lonesoulsurfer/Acid_Drip_Bassline_and_Drum_Synth/src/Acid_Drip_Drum_Acid_Drift_V5/Acid_Drip_Drum_Acid_Drift_V5.ino

/*
 * =====================================================================
 *              Acid Drip - RP2040 Acid Bassline Synthesizer
 *              Synthesis engine ported from reference "Badass Bass"
 * =====================================================================
 *
 * BUTTON LAYOUT (2 rows of 8 pads):
 *
 *   ┌─────┬─────┬─────┬─────┬─────┬─────┬──────┬──────┐
 *   │  1  │  2  │  3  │  4  │  5  │  6  │  7   │  8   │
 *   │step │step │step │step │step │step │step  │step  │
 *   │ 1   │ 2   │ 3   │ 4   │ 5   │ 6   │ 7    │ 8    │
 *   ├─────┼─────┼─────┼─────┼─────┼─────┼──────┼──────┤
 *   │  9  │ 10  │ 11  │ 12  │ 13  │ 14  │  15  │  16  │
 *   │KEY  │RIFF │SOUND│WALK │ FX  │TEMPO│PLEN  │PAT>  │
 *   └─────┴─────┴─────┴─────┴─────┴─────┴──────┴──────┘
 *   (bottom row labels only visible in FUNC mode)
 *

 * PAD FUNCTIONS (normal mode):
 *   Short press         : Toggle step on/off
 *   Long press ×1       : Toggle accent
 *   Long press ×2       : Toggle glide
 *   Hold + CUT pot      : Set step note (scale-quantised)
 *   All 16 pads are full steps — no dedicated buttons
 *
 * CHORD: PLAY (pads 1+2 simultaneously):
 *   Start / Stop sequencer
 *   Long hold (1s+)     : Factory reset
 *
 * CHORD: FUNC (pads 7+8 simultaneously):
 *   Toggle FUNC mode on/off
 *   Exits FX assign sub-mode if active
 *
 * SAVE / LOAD (while holding pads 7+8):
 *   Tap pad 3/4/5/6     : Load slot 1/2/3/4 — restores acid pattern, DRIFT,
 *                         and drum beat together, whichever of the three
 *                         actually have data saved in that slot
 *   Hold pad 3/4/5/6    : Save slot 1/2/3/4 (1 second hold) — captures
 *                         acid + DRIFT + drums together into that slot,
 *                         whatever each currently has dialled in. Same
 *                         gesture works from the drum screen too — either
 *                         screen saves/loads all three.
 *   Slot status shown as dots top-right of screen (yellow=saved, grey=empty)
 *
 * FUNC MODE (pads 7+8 to enter/exit):
 *   Bottom row pads 9-16 select a function (labels shown on screen):
 *     Pad 9  = KEY    — top row pads 1-8 select root note (C D Eb F G Ab Bb B)
 *     Pad 10 = RIFF   — pads 1-8 select preset riff pattern (DFLT/SQNCE/FUNK/MINI/JUMP/RAVE/SYNC/DARK)
 *     Pad 11 = SOUND  — top row pads 1-8 select synth voice
 *     Pad 12 = WALK   — top row pads 1-8 select note walk mode
 *                        p1=OFF  p2=4TH    p3=OCTWAVE p4=5TH
 *                        p5=BOUNCE  p6=MIN3RD  p7=VAMP3  p8=RANDOM
 *     Pad 13 = FX     — enters FX ASSIGN sub-mode
 *     Pad 14 = TEMPO  — top row pads 1-8 select preset BPM (100/110/120/128/133/138/145/160)
 *                        tap TEMPO pad repeatedly to set BPM by tap-tempo
 *     Pad 15 = PLEN   — top row pads 1-8 set length 1-8
 *                        bottom row pads 9-16 set length 9-16
 *     Pad 16 = PAT>   — top row pads 1-8 select pattern play mode:
 *                        p1=FWD  p2=CW (fwd then rev)  p3=ALT (odd/even)  p4=REV
 *                        p5=SKIP2 (every 2nd)  p6=SKIP3 (every 3rd)  p7=PING  p8=RND
 *
 * FX ASSIGN SUB-MODE (FUNC → pad 13):
 *   Phase 1: press top-row pads 1-8 to select an effect:
 *     Pad 1=None  Pad 2=Oct Up  Pad 3=Retrigger  Pad 4=Stutter
 *     Pad 5=Maj Step  Pad 6=Min Step  Pad 7=Dom7 Step  Pad 8=Dim Step
 *   Phase 2: press any pad 1-16 to assign that effect to that step
 *   Tap selected FX pad again to deselect
 *   Long-hold pad 1 = clear all step effects
 *   Pads 7+8 chord = exit FX assign to main screen
 *
 * EASTER EGG: ACID WALKS (pads 11+12+13+14, hold 1s):
 *   Toggles a hidden bank of 8 patterns inspired by classic acid/house
 *   tracks, each with its own preset key/tempo/length/sound.
 *   Pads 1-8 select a pattern. FUNC mode, FX assign, and drum mode all
 *   continue to work normally while active. Hold the same chord again
 *   to exit back to the normal pattern.
 *
 * ACCENT EDIT (pads 15+16, hold 1s):
 *   Toggles a mode where CUT/RES/DCY tune the accent envelope itself
 *   instead of the live filter:
 *     CUT = accent peak cutoff boost   RES = accent peak resonance boost
 *     DCY = accent decay-time (CCW=short/snappy, CW=long/dramatic)
 *   Normal CUT/RES/DCY values freeze while tuning. Hold the chord again
 *   to exit — settings save to EEPROM automatically and persist across
 *   power cycles until changed again.
 *
 * WIRING:
 *   TFT   : SCK=GP6, SDA=GP7, RST=GP8, DC=GP10, CS=GP13
 *   Pots  : CUT=GP26, RES=GP27, DCY=GP28
 *   Sync  : IN=GP2 (hold pad 14 at power-on to boot into Sync In mode)
 *   Audio : GP15 (100R + 10nF RC filter to output jack)
 *
 *   Pads (top row, steps 1-8 / FUNC apply):
 *     GP14=pad1  GP12=pad2  GP11=pad3  GP16=pad4
 *     GP17=pad5  GP19=pad6  GP20=pad7  GP21=pad8
 *
 *   Pads (bottom row, steps 9-16 / FUNC select):
 *     GP0=pad9   GP1=pad10  GP3=pad11  GP4=pad12
 *     GP5=pad13  GP9=pad14  GP18=pad15 GP22=pad16
 *
 * =====================================================================
 */

// =====================================================================
// MOZZI CONFIG - must precede all includes
// =====================================================================
#include "MozziConfigValues.h"
#define MOZZI_AUDIO_MODE     MOZZI_OUTPUT_PWM
#define MOZZI_ANALOG_READ    MOZZI_ANALOG_READ_NONE
#define MOZZI_AUDIO_PIN_1    15
#define MOZZI_AUDIO_RATE     16384
#define MOZZI_CONTROL_RATE   256

#include <Mozzi.h>
#include <SPI.h>
#include <Adafruit_GFX.h>
#include <Adafruit_ILI9341.h>
#include <EEPROM.h>
#include <math.h>   // expf/logf — ch2's decay-time-to-multiplier calc in triggerCh2Pulse()

// =====================================================================
// BENCH INSTRUMENTATION — TEMPORARY, pre-CHORD-engine only.
// =====================================================================
// Measures real spare headroom on core 0's audio path (this file's
// updateAudio(), GP15/acid) and core 1's audio path
// (BeatMachine2.ino's bmFillDrumBufferTo(), GP2/drift+drums) BEFORE any
// new engine work starts, so "how much CPU is actually free" is a
// measurement, not a guess.
//
// Deliberately does NOT touch flash-resident code from inside the
// __not_in_flash_func() audio functions: time_us_32() is a pico-sdk
// static inline that reads the hardware timer register directly (no
// call into flash), so it's safe to use here for the same reason the
// rest of updateAudio()/bmFillDrumBufferTo() has to stay flash-free —
// see the XIP-contention notes elsewhere in this file. Reporting
// (Serial prints, float math) happens ONLY from loop1() on core 1,
// never inside the timed sections themselves, so the act of measuring
// doesn't perturb what's being measured.
//
// Remove or set to 0 once the CHORD engine's core-placement and voice
// budget are decided — this isn't meant to ship.
#define BENCH_AUDIO_HEADROOM 1

#if BENCH_AUDIO_HEADROOM
#include "pico/time.h"

// One "window" = one second's worth of audio-rate samples, so reported
// numbers are already per-second — easy to eyeball without maths.
#define BENCH_WINDOW_SAMPLES MOZZI_AUDIO_RATE

// ---- core 0 (updateAudio / GP15 / acid) — written ONLY on core 0 ----
static uint32_t bench0_windowStart    = 0;
static uint32_t bench0_callsInWindow  = 0;
static uint32_t bench0_sumUsInWindow  = 0;
static uint32_t bench0_maxUsInWindow  = 0;

// Latest-window snapshot — updated once/sec, read by core 1's reporter.
// A torn read here costs at worst one stale field for one report cycle;
// this is a debug counter, not anything audio-critical, so that's fine.
volatile uint32_t bench0_avgUs  = 0;
volatile uint32_t bench0_maxUs  = 0;
volatile uint32_t bench0_callHz = 0;

// Call at the very top of updateAudio(), before any early return, so
// silent/idle samples still count — an average that only sees "busy"
// samples would understate real headroom.
static inline void __not_in_flash_func(benchAudioEnter)(uint32_t &t0) {
  t0 = time_us_32();
}

// Call at EVERY return point of updateAudio(), passing the t0 from
// benchAudioEnter(). No branches beyond the once-per-window reset, no
// allocation — kept cheap on purpose since this runs every sample.
static inline void __not_in_flash_func(benchAudioExit)(uint32_t t0) {
  uint32_t dt = time_us_32() - t0;
  bench0_callsInWindow++;
  bench0_sumUsInWindow += dt;
  if (dt > bench0_maxUsInWindow) bench0_maxUsInWindow = dt;
  if (bench0_callsInWindow >= BENCH_WINDOW_SAMPLES) {
    bench0_avgUs = bench0_sumUsInWindow / bench0_callsInWindow;
    bench0_maxUs = bench0_maxUsInWindow;
    uint32_t now  = time_us_32();
    uint32_t span = now - bench0_windowStart;   // real elapsed us this window
    bench0_callHz = span ? (bench0_callsInWindow * 1000000UL) / span : 0;
    bench0_windowStart   = now;
    bench0_callsInWindow = 0;
    bench0_sumUsInWindow = 0;
    bench0_maxUsInWindow = 0;
  }
}
#endif // BENCH_AUDIO_HEADROOM

// ── Beat Machine 2 — forward declarations ────────────────────────────
extern bool   bmMode;
extern bool   bmFullDirty;
extern void   bmInit();
extern void   bmUpdateControl();
extern void   bmDoDraw();
extern void   bmStartAudio();
int32_t       __not_in_flash_func(ch2RenderSample)();   // DRIFT render — defined in Drift.ino; RAM-resident, see there
extern bool   bmAlarmStarted;  // true once GP2 audio hardware is initialized —
                               // gates every bmFillDrumBuffer call (NOT debug)
extern void   bmClearPadState();
extern bool   bmPotLocked;
extern uint8_t bmPotPickup;
extern void     bmTriggerStep(uint8_t step);
extern byte     bmStepDiv;
extern byte     bmPulseNum;
extern uint16_t bmStepNum;
extern byte     bmDrumPos;
extern bool   bmPlaying;
extern bool   bmPlayChanged;
extern void   bmFillDrumBuffer();
extern int32_t bmRenderDrumSample();  // one drum-bus sample (GP15 fold-in for sync mode)
extern void   bmFillDrumBufferMax();  // full pre-fill — ONLY for EEPROM.commit() (both cores
                                      // stall during flash erase, fills can't be threaded).
                                      // Never use before draws: see bmFillScreenFed()
extern void   bmPrintFed(const char* s);
extern void   bmFillScreenFed(uint16_t color);  // banded full-screen clear — ALWAYS use
                                                // instead of tft.fillScreen() once audio is
                                                // running; the atomic ~103ms clear both
                                                // underruns GP2 and XIP-stalls core 0/Mozzi  // print char-by-char, topping up GP2 between chars —
                                          // REQUIRED for any string over ~20 chars: one atomic
                                          // print() of a long string is 40-80ms of per-pixel GFX
                                          // SPI, which outspends the ring buffer in a single call
extern void   bmDrawDrumFlash();
extern uint32_t bmLastFlashDraw;
extern float    bmStoredTempo;
extern bool     bmPChord[16];
extern bool     bmPState[16];
extern bool     bmP11Deferred;
extern void   bmSavePatch(uint8_t slot);
extern void   bmLoadPatch(uint8_t slot);
extern bool   bmPatchWasPlaying(uint8_t slot);
extern void   bmStartDrums();
extern void   bmStopDrums();
extern bool   bmSlotHasData[4];
extern void   bmCheckSlots();
extern void   bmResetToBasic();

#define BM_SW_A  8   // pad 9 (index 8) — mode switch pad A
#define BM_SW_B  9   // pad 10 (index 9) — mode switch pad B
bool     bmAcidWasRunning = false;  // legacy — no longer used for logic (kept to avoid extern breakage)
// acidPlaying: true when the acid sequencer should fire notes AND render
// on GP15 (see updateAudio() — GP15 is acid-only; DRIFT lives on GP2).
// Independent of bmPlaying and of driftPlaying.
// seq.running = acidPlaying || driftPlaying || bmPlaying — the shared clock
// ticks whenever ANY module wants it, and stopping one never kills another's
// clock.
bool     acidPlaying      = false;

// driftPlaying: DRIFT's own play/stop state, exactly mirroring acidPlaying
// but for the DRIFT voice, which renders on GP2 (bmFillDrumBufferTo() in
// BeatMachine2.ino, summed with drums there) — see the DRIFT OUTPUT
// comment near ch2SynthMode's declaration. Acid and DRIFT can play
// SIMULTANEOUSLY, blended by the PCB's physical mix pot; pads 9+10+11 swap
// ch2SynthMode, which decides which one the pad/pot surface currently
// EDITS, not which one is audible. Each has its own independent play/stop
// state, which is why this can't just reuse acidPlaying: start acid, swap
// edit focus to DRIFT (9+10+11), start DRIFT too (pads 1+2) — both should
// now be audible together (mix pot permitting), and stopping one (pads 1+2
// again) must not touch the other's state.
bool     driftPlaying     = false;


// Easter egg: hold pads 11+12+13+14 (indices 10-13) together for ~1s to
// toggle "Acid Walks" — a value strip of 8 classic-acid-inspired patterns.
#define WALK_PAD_A 10  // pad 11
#define WALK_PAD_B 11  // pad 12
#define WALK_PAD_C 12  // pad 13
#define WALK_PAD_D 13  // pad 14
#define WALK_HOLD_MS 1000
bool     walksMode    = false;  // true while the Acid Walks value strip is shown
bool     walksArmed   = false;  // chord held, waiting for WALK_HOLD_MS
uint32_t walksArmMs   = 0;
uint8_t  curWalk      = 0;      // currently-loaded Acid Walks pattern index

// PATTERN CHAINING: quick double-tap of pads 12+13 (indices 11-12 — reuses
// two of the four WALK pads) toggles between:
//   - chain-build mode: pads 3-6 (slots 1-4) tap-append to a play order,
//     up to 16 positions, repeats allowed
//   - chain playback: on exit, the built chain auto-plays, advancing to
//     the next chain position after each slot's pattern completes one
//     full loop (tick-counted against seq.len, so it works under any
//     rrMode, not just plain FWD)
// Session-only — not saved to EEPROM. Tapping the gesture again at any
// time (whether currently building or currently chain-playing) drops
// whatever chain exists and starts a fresh build.
//
// This DOES collide with the WALK chord in practice, despite reusing only
// 2 of its 4 pads: a real "press all 4 together" gesture routinely lands
// 12+13 within each other's 200ms double-tap window before 11 and 14 also
// register, since WALK's own arm check only looks at whether all 4 are
// down AT THE INSTANT of a press — it has no way to tell "12+13 just
// landed, but this might still be the start of a 4-pad gesture" from "12+13
// was a deliberate standalone double-tap". CHAIN_HOLD_MS below exists
// solely to give WALK's other two pads a chance to prove it's the latter
// before CHAIN commits — see the arm/fire logic in updateControl() and the
// press-time chord check for the reasoning in full.
#define CHAIN_PAD_A WALK_PAD_B  // pad 12
#define CHAIN_PAD_B WALK_PAD_C  // pad 13
#define CHAIN_HOLD_MS 150       // short — long enough for a genuine 4-finger
                                 // WALK attempt to have landed pad 11 and/or
                                 // pad 14 too, short enough that a deliberate
                                 // double-tap toggle still feels immediate
bool     chainMode      = false;  // chain-builder UI/input active
bool     chainArmed     = false;  // 12+13 landed, waiting out CHAIN_HOLD_MS
uint32_t chainArmMs     = 0;
bool     chainActive    = false;  // a built chain is currently playing back
uint8_t  chain[16]      = {0};    // slot index (0-3) per chain position
uint8_t  chainLen       = 0;      // number of filled chain positions
uint8_t  chainPos       = 0;      // current playback position within the chain
uint16_t chainTickCount = 0;      // steps elapsed since the last chain advance

// ACCENT — was previously live-tunable (hold pads 15+16, tweak on CUT/RES/
// DECAY). Locked to a fixed value instead: the difference it made was
// small, and it freed pads 15+16 for MIX EDIT below.
// ---- Filter envelope depth (303 "wah"/squelch sweep) ----------------------
// The squelch is the cutoff ENVELOPE sweeping the filter, not static
// resonance. These set how far the filter opens on note-on before decaying
// back down. They were tiny (30/40 cutoff, 0/200 res) — a nudge, not a sweep —
// which is why hardware never sounded like the reference render. Deepened here.
// IMPORTANT: the envelope ADDS to the CUT pot. For the sweep to be audible you
// must play with the CUT pot LOW (dark rest) so the envelope has room to open
// it — exactly like a real 303 (cutoff down, env-mod up). With CUT high the
// envelope just slams into the 255 ceiling and you hear no wah.
#define ENV_CUTOFF_NORMAL    90    // SEED: normal-note cutoff env peak — sweep depth
#define ENV_RES_NORMAL       50    // normal-note resonance env peak (fixed, not a knob)
#define ACCENT_RES_FIXED    200    // accent peak resonance boost (capped at gResCap in the cascade)
#define ENV_DECAY_NORMAL      5    // SEED: normal env decay divisor (HIGHER = slower/longer sweep)
#define ACCENT_DECAY_FIXED   10    // accent envelope decay divisor (1-20) — "mid"
#define ACID_LPF_RESDIV_SEED 200   // SEED: resonance divisor, moderate default in musical range 150-256

// ---- Runtime-tweakable filter params (SETTINGS mode: hold pads 1+2+3) ------
// These start at the SEED values above and are overwritten by EEPROM on boot
// if a saved block exists. In SETTINGS mode the three pots drive them live:
//   CUT pot   -> gEnvCutNorm  (sweep DEPTH; accent auto-scales to 2x, capped 255)
//   DECAY pot -> gEnvDecayDiv (sweep SPEED; higher divisor = slower "waaow")
//   RES pot   -> gResDiv      (resonance; gResCap auto-tracks at x1.4 so the
//                              cascade can never reach the ~8kHz squeal band)
int16_t gEnvCutNorm  = ENV_CUTOFF_NORMAL;
int16_t gEnvDecayDiv = ENV_DECAY_NORMAL;
int16_t gResDiv      = ACID_LPF_RESDIV_SEED;
int16_t gResCap      = (ACID_LPF_RESDIV_SEED * 7) / 5;   // recomputed whenever gResDiv changes
int16_t gResTrim     = 110;   // HP-filter input body-trim, driven by the front RES pot (110=full body)
// recomputeResCap only feeds the CASCADE fallback's squeal cap now; the HP
// filter's resonance + body-trim come live from the front-panel RES pot
// (gAcidResCoeffQ8 / gResTrim, set in updateControl).
static inline void recomputeResCap() {
  gResCap = (int16_t)((gResDiv * 7) / 5);
}

// ---- SETTINGS mode: hold pads 1 + 9 for ~1s (mirrors MIX EDIT) ------------
// 1 & 9 are physically adjacent and free as a pair — 1+2 is the PLAY chord and
// 9+10 is the LAYER chord, but 1+9 isn't claimed by anything.
#define SET_PAD_A 0    // pad 1
#define SET_PAD_B 8    // pad 9
#define SET_HOLD_MS 1000
bool     setEditMode  = false;   // true while CUT/RES/DECAY pots trim filter params
bool     setEditArmed = false;   // chord held, waiting for SET_HOLD_MS
uint32_t setEditArmMs = 0;
int      setPotSnap[3] = {-1,-1,-1};        // raw pot at entry (soft takeover)
bool     setPotLive[3] = {false,false,false};

// MIX EDIT: hold pads 15+16 (indices 14-15) together for ~1s to toggle a
// mode where the CUT/RES/DECAY pots trim the output level of each of the
// three synth engines independently — CUT=acid, RES=DRIFT, DECAY=drums.
// This is a DIGITAL trim on top of the physical summing pot (which only
// blends acid/GP15 against DRIFT+drums/GP2 as one combined pair) — it's
// what actually lets DRIFT be balanced against drums, which the pot alone
// can't do. Values save to EEPROM on exit, same pattern accent used to.
#define MIX_PAD_A 14  // pad 15
#define MIX_PAD_B 15  // pad 16
#define MIX_HOLD_MS 1000
bool     mixEditMode  = false;  // true while CUT/RES/DECAY pots trim engine levels
bool     mixEditArmed = false;  // chord held, waiting for MIX_HOLD_MS
uint32_t mixEditArmMs = 0;
// POT PICKUP. Without this, entering MIX EDIT snapped all three levels to
// wherever the physical pots happened to be sitting — so the saved mix you
// came in to inspect was destroyed by the act of opening the page, and you
// could not nudge one engine without the other two jumping too. Each pot
// now stays inert until it is MOVED past a threshold from its position at
// entry, so opening MIX EDIT is non-destructive and you adjust exactly the
// engine you touch. Same soft-takeover idea as the drum machine's
// bmFillPotLock/bmFillPotRef pair.
int      mixPotSnap[3] = {-1,-1,-1};   // raw pot at entry; -1 = not yet armed
bool     mixPotLive[3] = {false,false,false};
// Set true while in drum mode. Drums bypass the per-engine pot-ownership
// block (updateControl returns at the bmMode guard, above it), so a
// synth->drums->synth round trip never trips that block's ctx-change test
// and the still-live pots overwrite the stored values on return. This flag
// forces the pickup to re-arm the first time we're back in acid/DRIFT.
bool     gPotCtxReArm = false;
#define  MIX_PICKUP_DELTA 24           // raw ADC counts (~2.3% of travel)
// Same threshold reused by the per-engine pot ownership in updateControl().
#define  POT_PICKUP_DELTA MIX_PICKUP_DELTA
// MIX_UNITY: the raw 0-255 level value that means "unchanged, original
// volume". It is now the SAME for all three engines, so all three pots
// behave identically: unity at 2/3 travel, attenuation below, up to ~1.5x
// boost above.
//
// Acid used to be the exception — unity pinned at the TOP of its travel,
// attenuate-only — because its raw waveform rides close to full 0-255
// scale and any boost hard-clipped into buzzing. That asymmetry is why
// mixing acid felt worse than mixing drums or DRIFT: its pot had a
// different neutral position from the other two, and it could only ever
// be pulled DOWN, never pushed up against them. The fix is to give acid
// the soft-clip limiter that DRIFT and drums already have (see the acid
// gain block in updateAudio), which buys the same clean headroom they
// use — so the special case can go entirely.
#define MIX_UNITY       170   // all three engines: unity at 2/3 travel
uint8_t  mixAcidLevel  = MIX_UNITY;   // 0-255 raw pot position — persisted/displayed as-is
uint8_t  mixDriftLevel = MIX_UNITY;
uint8_t  mixDrumLevel  = MIX_UNITY;
// Derived Q8 gain constants actually applied at audio rate (256 = unity).
// Recomputed by recomputeMixGains() whenever a level above changes —
// keeps the division out of the audio-rate render paths.
uint16_t mixAcidGainQ8  = 256;
uint16_t mixDriftGainQ8 = 256;
uint16_t mixDrumGainQ8  = 256;
// SQUARE-LAW taper below unity, linear boost above it.
//
// These were linear in amplitude, which is a poor fader law because
// hearing is logarithmic: measured over acid's travel, the top HALF of
// the pot spanned only 6 dB — it felt like nothing was happening — while
// everything audible was crammed into the bottom fifth, where it dropped
// off a cliff. Squaring approximates a log taper for one multiply: half
// travel becomes -12 dB instead of -6, quarter travel -24 instead of -12.
// That spreads the useful range across the whole sweep, which is the
// single biggest reason these pots felt hard to set.
static uint16_t mixGainFor(uint8_t level, uint8_t unity) {
  if (level >= unity) {
    if (unity >= 255) return 256;                                  // no room to boost
    uint32_t over = ((uint32_t)(level - unity) * 128U) / (255U - unity);
    return (uint16_t)(256 + over);                                 // unity .. ~1.5x
  }
  uint32_t norm = ((uint32_t)level * 256U) / unity;                // 0..255 below unity
  return (uint16_t)((norm * norm) >> 8);                           // square law
}
void recomputeMixGains() {
  mixAcidGainQ8  = mixGainFor(mixAcidLevel,  MIX_UNITY);
  mixDriftGainQ8 = mixGainFor(mixDriftLevel, MIX_UNITY);
  mixDrumGainQ8  = mixGainFor(mixDrumLevel,  MIX_UNITY);
}



// =====================================================================
// PINS
// =====================================================================
#define TFT_CS    13
#define TFT_RST    8
#define TFT_DC    10
#define TFT_MOSI   7
#define TFT_SCK    6
#define POT_CUT   26
#define POT_RES   27
#define POT_DECAY 28
#define SYNC_IN    2

// SYNC IN pulse detection — interrupt-driven, not polled. DIN-sync-style
// clock pulses (24 PPQN, the TB-303/909 standard) are commonly only 1-2ms
// wide; polling at MOZZI_CONTROL_RATE (~3.9ms/cycle, see below) risks
// missing narrow pulses entirely, especially at higher tempos. An ISR
// catches every rising edge regardless of width or CPU timing; the
// control-rate code just checks and clears this flag once per cycle.
volatile bool     gSyncPulseFlag  = false;
volatile uint32_t gSyncPulseMicros = 0;   // micros() at the last rising edge —
                                          // stamped in the ISR so tempo isn't
                                          // quantized to the 256Hz control loop.
void syncPulseISR() { gSyncPulseMicros = micros(); gSyncPulseFlag = true; }

// 16 pads — top row (steps 1-8): applies FUNC values / FX assign phase 1+2
//           bottom row (steps 9-16): selects FUNC function in FUNC mode
// Chord: pads 1+2 (indices 0+1) = PLAY/STOP, pads 7+8 (indices 6+7) = FUNC toggle
const uint8_t PAD_PINS[16] = {
  14,12,11,16,17,19,20,21,   // pads 1-8  (steps 1-8,  top row) — pad1=GP14, pad3=GP11 (swapped)
   0, 1, 3, 4, 5, 9,18,22    // pads 9-16 (steps 9-16, bottom row)
};

#define PAD_PLAY_A  0   // pads 1+2 pressed together = PLAY/STOP
#define PAD_PLAY_B  1
#define PAD_FUNC_A  6   // pads 7+8 pressed together = FUNC toggle
#define PAD_FUNC_B  7

// =====================================================================
// DISPLAY
// =====================================================================
#define SW 320
#define SH 240

// This forces MADCTL's MY (Y-mirror) bit on top of setRotation(3)'s own
// MADCTL value. Reason unconfirmed — possibly needed for a specific panel
// variant with reversed row addressing, but that has NOT been verified.
// What IS confirmed: on a standard ILI9341 panel this fights with
// setRotation(3) and produces the wrong orientation (see repo issue #2).
// Comment this out if your screen looks wrong after setRotation(3) with
// it enabled.
#define PANEL_NEEDS_Y_MIRROR

// Colour palette (RGB565)
#define C_BG    0x0000
#define C_WHT   0xFFFF
#define C_RED   0xF800
#define C_GRN   0x07E0
#define C_YEL   0xFFE0
#define C_CYN   0x07FF
#define C_ORG   0xFC60
#define C_DGR   0x4208
#define C_MGR   0x8410
#define C_BLU   0x001F
#define C_MGN   0xF81F  // magenta — accent indicator

// Step-grid colors (303-style warm amber, replacing plain greys for step cells)
#define C_AMB   0xFC60  // orange — active note bar fill, cursor cell background (matches title 'I')
#define C_AMBBG 0x3922  // dark amber-brown — active step cell background (non-cursor)
#define C_AMBBR 0x59C2  // amber-brown — empty step cell border
// DRIFT-EDIT step tints — subtle TEAL-shifted versions of the amber cell
// colours, shown ONLY while ch2EditMode is active (the "you are editing
// DRIFT" signal). Green raised, blue kept LOW: this is the key correction.
// The first version cooled toward blue, which collided with the azure
// trigger RING (0x04BF, blue-dominant) — a ringed step in edit was
// blue-on-blue and the ring vanished. Teal (green-dominant) is a clearly
// different hue from the ring's blue, so both read at once. Backgrounds/
// border only; rings, note bars and the bright playhead cell unchanged.
#define C_DR_BR  0x3AC5  // empty border  (teal, was C_AMBBR)
#define C_DR_BG  0x1A25  // inactive bg   (teal, was C_AMBBG)
#define C_DR_ACC 0x110C  // accent bg     (was C_MGND)
#define C_MGND  0x3009  // dark magenta — accent step cell background
#define C_CH2   0x04BF  // azure — channel-2 identity: trigger ring
                        // (drawStepCellEx) + ch2 FUNC value-strip tiles.
                        // Colour history, so nobody repeats it:
                        //  - C_ORG rejected: same 0xFC60 value as C_AMB —
                        //    an orange ring vanishes on active cells.
                        //  - violet 0xA81F rejected ON HARDWARE: it is
                        //    R21/G0/B31 vs accent magenta's R31/G0/B31 —
                        //    literally dim magenta, indistinguishable from
                        //    accent steps at arm's length.
                        // Azure (0,150,255) has ZERO red so it cannot muddle
                        // with the magenta family, sits between deep blue
                        // (0x001F, dim label borders) and cyan (0x07FF,
                        // small glide/FX dots) with clear daylight to both,
                        // and is near-complementary to amber — it pops
                        // hardest on exactly the cells that matter.

Adafruit_ILI9341 tft = Adafruit_ILI9341(&SPI, TFT_DC, TFT_CS, TFT_RST);

// =====================================================================
// NOTE FREQUENCY TABLE
// =====================================================================
// Placed in RAM (see updateAudio comment) — avoids XIP contention with core 1's SPI traffic
const uint16_t __not_in_flash("audiotables") noteFreq[60] = {
  274,291,308,326,346,366,388,411,436,461,489,518,
  549,581,616,652,691,732,776,822,871,923,978,1036,
  1097,1163,1232,1305,1383,1465,1552,1644,1742,1845,1955,2071,
  2195,2325,2463,2610,2765,2930,3104,3288,3484,3691,3910,4143,
  4389,4650,4927,5220,5530,5859,6207,6577,6968,7382,7821,8286,
};

// =====================================================================
// WAVETABLES
// =====================================================================
const uint8_t __not_in_flash("audiotables") sinetable[256] = {
  127,130,133,136,139,142,145,148,151,154,157,160,163,166,169,172,
  175,178,181,184,186,189,192,194,197,200,202,205,207,209,212,214,
  216,218,221,223,225,227,229,230,232,234,235,237,239,240,241,243,
  244,245,246,247,248,249,250,250,251,252,252,253,253,253,253,253,
  254,253,253,253,253,253,252,252,251,250,250,249,248,247,246,245,
  244,243,241,240,239,237,235,234,232,230,229,227,225,223,221,218,
  216,214,212,209,207,205,202,200,197,194,192,189,186,184,181,178,
  175,172,169,166,163,160,157,154,151,148,145,142,139,136,133,130,
  127,123,120,117,114,111,108,105,102,99,96,93,90,87,84,81,
  78,75,72,69,67,64,61,59,56,53,51,48,46,44,41,39,
  37,35,32,30,28,26,24,23,21,19,18,16,14,13,12,10,
  9,8,7,6,5,4,3,3,2,1,1,0,0,0,0,0,
  0,0,0,0,0,0,1,1,2,3,3,4,5,6,7,8,
  9,10,12,13,14,16,18,19,21,23,24,26,28,30,32,35,
  37,39,41,44,46,48,51,53,56,59,61,64,67,69,72,75,
  78,81,84,87,90,93,96,99,102,105,108,111,114,117,120,123
};

const uint8_t __not_in_flash("audiotables") noisetable[64] = {
  232,175,188,102,142,3,70,116,17,139,22,155,54,118,84,22,
  251,228,160,233,30,32,6,125,16,216,122,189,95,232,135,205,
  181,97,90,80,76,170,0,4,123,183,46,163,185,40,47,208,
  145,67,219,87,74,140,213,10,72,51,29,142,230,63,204,123
};

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
  415,417,418,420,421,423,424,426,427,429,430,432,433,435,436,438,
  439,441,442,444,446,447,449,450,452,453,455,456,458,459,461,462,
  464,465,467,469,470,472,473,475,476,478,480,481,483,484,486,487,
  489,491,492,494,495,497,498,500,502,503,505,506,508,508,508,508,
};

const int soundRange[11][4] = {
  // {RES min, RES max, CUT min, CUT max}. CUT min>max would REVERSE the
  // pot for that sound. Sound 7 was the only one written that way
  // (1023,0), so on NOISE+COMB alone the cutoff pot ran backwards —
  // clockwise closed the filter while every other sound opened it. Fixed
  // to 0,1023 to match the other ten. The "CUT reversed" notes on 4/5/6
  // were also wrong: those rows are 0->1020, i.e. not reversed at all.
  {718,200,  70,1020},   // 0  SAW+LPF
  {670,260,  80,670},    // 1  SQR+LPF
  {670,0,    0,1020},    // 2  SINE+LPF
  {670,270,  80,1020},   // 3  NOISE+LPF
  {1020,250, 0,1020},    // 4  CSAW  — RES reversed
  {1023,0,   0,1023},    // 5  CSQR  — RES reversed
  {1020,600, 0,1020},    // 6  CSIN  — RES reversed
  {1023,0,   0,1023},    // 7  NOISE+COMB — RES reversed (CUT was 1023,0: fixed)
  {1023,0,   0,1023},    // 8  PWM
  {1023,0,   0,1023},    // 9  SUB SQUARE — RES=filter resonance(reversed), CUT=sub mix
  {0,1023,   0,1023},    // 10 WAVESHAPE
};

int restrictValue(int val, int mn, int mx) {
  long temp = mx - mn;
  temp *= (val < 0 ? 0 : (val > 1023 ? 1023 : val));
  temp /= 1023;
  return (int)(temp + mn);
}

// =====================================================================
// SYNTHESIS STATE
// =====================================================================
volatile uint16_t gFreq      = 287;
volatile uint16_t gTarget    = 287;
volatile int32_t  gFreqFP    = 287 << 8;  // 8.8 fixed-point; gFreq = gFreqFP >> 8
volatile int32_t  gGlideStep = 0;
volatile bool     gGlide     = false;
volatile bool     gPorta     = false;     // portamento — reserved for future use
volatile uint8_t  gPortaSpeed= 4;

volatile int16_t  gCutoff           = 64;
volatile int16_t  gCutoffDisplay    = 64;   // 0-255 for bar display (raw pot, no envelope)
volatile int16_t  gResonance        = 0;
volatile int16_t  gResonanceDisplay = 512;  // 0-1023 for bar display (512 = mid)

// STEP-HIGHLIGHT TRACKING — a single shared source of truth for "which
// step cell is currently drawn as highlighted", used by drawMain()'s full
// redraw, updateMain()'s incremental chase, and loop1()'s inline chase.
// Previously these each kept their own independent static tracker, which
// desynced whenever a full redraw (e.g. an automatic chain-pattern switch)
// interrupted the normal per-tick chase: drawMain()'s 16-cell loop takes
// real time to run, and since drawStepCell() checks seq.cur live on every
// call, whichever cell coincided with seq.cur at ITS OWN draw moment got
// highlighted — but no other tracker knew about it, so it never got erased
// and stayed lit indefinitely. gDisplayCurOverride freezes seq.cur for the
// duration of drawMain()'s loop so exactly one cell is highlighted per
// pass, and gHighlightedStep is the single shared "last known highlighted
// cell" used everywhere so any tracker can correctly erase it later.
int16_t  gDisplayCurOverride = -1;   // >=0 while drawMain()'s loop is running
uint8_t  gHighlightedStep    = 255;  // 255 = none highlighted yet
bool     gSkipMainScreenClear = false;  // one-shot: skip drawMain()'s fillScreen() when
                                          // already on the main screen (no other screen's
                                          // remnants to wipe) — set before an in-place
                                          // refresh like a chain auto-advance to cut TFT time

volatile int16_t  gVolSub    = 500;
volatile int16_t  gEnvCutoff = 0;    // envelope filter boost — peaks on note-on, decays with DCY
volatile int16_t  gEnvRes    = 0;    // accent resonance envelope boost — peaks on accented note-on, decays with DCY
volatile bool     gAccentActive = false;  // true while the current note's accent envelope is decaying
volatile uint8_t  gSound     = 0;
volatile uint8_t  gEffect    = 0;
volatile int16_t  gDecaySpeed= 2;
int16_t  lastDecaySpeed = 2;  // frozen gDecaySpeed value while mixEditMode is active
volatile uint32_t gLastStepMs= 0;

static uint16_t cnt = 0;
volatile int16_t filtA = 0;
volatile int16_t filtB = 0;
// 303-style 24 dB/oct filter for the LPF sounds (0/1/2/3/8/9). Built as TWO of
// the original proven-squelchy 2-pole SVF stages in series (filtA/filtB =
// stage 1, filtA2/filtB2 = stage 2). This replaced an int32 4-pole ladder that
// could NOT self-oscillate in this 8-bit fixed-point env — force-maxed it only
// reached ~1/4 the amplitude the 2-pole rails to, so it never squelched on
// hardware however it was tuned. The cascade keeps the topology that actually
// resonates here and just doubles the slope. Set ACID_LPF_4POLE to 0 to fall
// back to the single 2-pole (12 dB/oct) in one line.
#define ACID_LPF_4POLE 1
volatile int16_t filtA2 = 0, filtB2 = 0;
// ---- Higher-precision filter (ACID_LPF_HP) --------------------------------
// Same dual-2-pole SVF topology, but run with Q8 int32 states so the resonant
// peak can build past the old +/-127 wall, then a SOFT-CLIP maps it to 8-bit so
// the peak saturates musically instead of hard-clipping/buzzing. This is what
// finally gives RES an audible, cutoff-tracking sweep (~4.5->9 dB vs the old
// filter's flat ~3.5 dB) and makes drive usable. RES trades a little body for
// the peak (gResTrim) — correct resonant-filter behaviour. Set to 0 to fall
// back to the 8-bit cascade above for an instant A/B on hardware.
#define ACID_LPF_HP 1
#define ACID_HP_CUT_MAX  170   // HP cutoff ceiling. Scream flavour "C": raised from 150 so DPTH opens
                               // brighter and the resonant peak sits high enough to bite when hard-
                               // clipped, still short of the Nyquist alias-squeak zone.
#define ACID_HP_RES_MAX  270   // HP resonance coefficient ceiling (Q8; 270/256 = 1.05). Past ~0.90 the
                               // hard-clipped peak SCREAMS (303-style) rather than just resonating.
                               // Front-panel RES pot drives up to here (see gAcidResCoeffQ8).
volatile int32_t HA1 = 0, HB1 = 0, HA2 = 0, HB2 = 0;   // Q8 states
volatile int16_t gAcidResCoeffQ8 = 60;   // HP resonance coefficient (Q8), live from the front RES pot
volatile int16_t gSlopeBlend = 255;      // HP filter slope: 0 = 12dB/oct (rounder), 255 = 24dB/oct (steeper). Fixed at 24dB now.
volatile int16_t gHpCutMax   = ACID_HP_CUT_MAX;  // live HP cutoff ceiling = TONE/brightness (SETTINGS RES lane), 110..190
#define ACID_LPF_QLIM (600 << 8)                        // state ceiling (headroom for the peak)
// Musical soft-clip: linear body up to +/-96, smooth knee to +/-127, then ceiling.
static inline int32_t acidSoftClip(int32_t x) {
  int32_t a = x < 0 ? -x : x, y;
  if      (a <= 96)  y = a;
  else if (a <= 480) y = 96 + (((a - 96) * 42) >> 9);
  else               y = 127;
  return x < 0 ? -y : y;
}
static uint8_t   combBuf[256];
static uint8_t   combPtr = 0;

volatile uint32_t lfoPos   = 0;
volatile int      lfoOffset= 0;
volatile uint8_t  phaseSw  = 128;

volatile uint16_t vFreq[8];
volatile uint16_t vCnt[8];
volatile uint16_t subFreq = 144;  // Sub Square oscillator frequency = gFreq/2 (sound 9)
volatile uint16_t subMix  = 0;    // Sub Square mix balance 0-1023 (sound 9)
static uint16_t subCnt = 0;       // Sub Square phase accumulator
volatile uint8_t  numV  = 1;
volatile uint8_t  volStd= 128;
volatile uint8_t  volClp= 128;

const int8_t __not_in_flash("audiotables") arpeggio[4][4] = {
  {0, 4, 7, 12},
  {0, 3, 7, 12},
  {0, 4, 7, 11},
  {0, 3, 6,  9},
};

// =====================================================================
// SEQUENCER
// =====================================================================
#define NUM_STEPS 16

struct Step {
  uint8_t note;
  bool    active;
  bool    accent;
  bool    glide;
  uint8_t effect;
};

struct Sequencer {
  Step    steps[NUM_STEPS];
  uint8_t origNote[NUM_STEPS];  // working notes — rootNote transposed to current key
  uint8_t rootNote[NUM_STEPS];  // permanent store — always relative to key=C, never mutated
  uint8_t cur;
  uint8_t len;
  bool    running;
  uint16_t tempo;
  uint32_t interval;
  uint32_t lastUs;
  uint8_t  octave;
  uint8_t  sound;
  int8_t   trans;
  uint8_t  arpPos;
  uint8_t  key;
  uint8_t  scale;
  uint8_t  algo;
};

// =====================================================================
// PRESET PATTERNS  (8 baked-in acid riffs, absolute semitones key=C)
// =====================================================================
#define NUM_PRESETS 8
struct PresetPattern {
  uint8_t note[16];
  uint8_t flags[16];   // bit0=active, bit1=accent
  uint8_t glide[16];
  uint8_t effect[16];
};

const PresetPattern PRESETS[NUM_PRESETS] = {
// P0: DFLT — original default riff
{ {24,24,24,27,24,36,31,29,24,31,29,31,36,24,36,39}, {1,1,1,1,1,1,1,1,1,1,1,1,1,1,1,1}, {0,0,0,0,0,0,0,0,0,0,0,0,0,0,0,0}, {0,0,0,0,0,0,0,0,0,0,0,0,0,0,0,0} },
// P1: SQNCE — tight 8-step motif looped twice, accent-glide pairs on push notes
{ {24,24,31,24,29,27,24,29,24,24,31,24,29,27,24,29}, {3,0,1,0,3,1,0,1,3,0,1,0,3,1,0,1}, {0,1,0,0,0,1,1,0,0,1,0,0,0,1,1,0}, {0,0,0,0,0,0,0,0,0,0,0,0,0,0,0,0} },
// P2: FUNK — sparse, punchy, lots of rests
{ {24,24,24,27,24,24,31,24,29,24,24,27,24,31,29,24}, {3,0,0,1,0,1,3,0,3,0,0,1,0,1,1,3}, {0,0,0,0,0,0,0,0,0,0,0,1,0,0,1,0}, {0,0,0,0,0,0,0,0,0,0,0,0,0,0,0,0} },
// P3: MINI — hypnotic minimal loop with one accent shift
{ {24,24,27,24,24,27,24,29,24,24,27,24,29,31,29,27}, {1,1,1,1,1,1,1,3,1,1,1,1,1,3,1,1}, {0,0,1,0,0,1,0,0,0,0,1,0,0,0,1,0}, {0,0,0,0,0,0,0,0,0,0,0,0,0,0,0,0} },
// P4: JUMP — octave leaps, big energy
{ {24,36,24,36,27,39,27,31,24,36,29,36,24,34,36,24}, {3,1,1,1,3,1,1,1,3,1,1,1,3,1,1,3}, {0,0,0,1,0,0,0,0,0,0,1,0,0,0,1,0}, {0,0,0,0,0,0,0,0,0,0,0,0,0,0,0,0} },
// P5: RAVE — pumping 16th notes, heavy accents, octave hits, all active
{ {24,36,24,27,36,24,34,36,24,36,27,36,29,36,34,39}, {3,1,3,1,3,1,3,1,3,1,3,1,3,1,3,3}, {0,0,0,0,0,0,0,0,0,0,0,0,0,0,0,0}, {0,0,0,0,0,0,0,0,0,0,0,0,0,0,0,0} },
// P6: SYNC — syncopated off-beat accents and rests
{ {24,24,24,29,27,24,31,29,24,27,24,29,31,31,34,36}, {0,3,0,1,3,0,1,1,0,3,0,1,3,0,1,3}, {0,0,0,0,0,0,1,0,0,0,0,1,0,0,0,0}, {0,0,0,0,0,0,0,0,0,0,0,0,0,0,0,0} },
// P7: DARK — sparse minor, chromatic Ab passing note at step 13, rests give space to brood
{ {24,24,27,24,29,27,24,29,24,27,24,27,32,31,29,27}, {3,0,1,0,3,1,0,1,3,1,0,1,3,1,1,3}, {0,1,0,0,0,1,1,0,0,0,0,1,0,0,1,0}, {0,0,0,0,0,0,0,0,0,0,0,0,0,0,0,0} },
};

uint8_t curPreset = 0;

// =====================================================================
// EASTER EGG — "ACID WALKS" (8 patterns inspired by classic acid/303 tracks)
// Hold pads 11+12+13+14 together for ~1s to activate. Same PresetPattern
// layout as PRESETS above (absolute semitones, key=C). These are original
// interpretations in the spirit of each track, not transcriptions.
// =====================================================================
#define NUM_WALKS 8
const PresetPattern WALK_PATTERNS[NUM_WALKS] = {
// W0: DAFNK — Daft Punk "Da Funk"-style: the real 303 riff is in G minor,
// using only G (root), A#/Bb (m3), C (4th), D#/Eb (m6), and F (m7) — D and
// A are omitted. The famous opening is a single rest on step 1 (the "only
// muted note... creates a very effective rest... every time it loops"),
// with an octave turnaround to G3 on the last step before looping back.
{ {31,31,34,31,29,31,34,36, 31,31,27,31,34,29,31,43}, {0,1,1,1,3,1,1,1,3,1,1,1,3,1,1,3}, {0,0,1,0,0,0,1,0,0,0,1,0,0,0,1,0}, {0,0,0,0,0,0,0,0,0,0,0,0,0,0,0,2} },
// W1: ACIDTR — Phuture "Acid Tracks"-style: 8-step near-static hypnotic
// core (the magic in the original comes from live filter/resonance tweaks
// on a near-static loop, not the notes), steps 8-15 a subtle variation
{ {24,24,24,24,27,24,24,24, 24,24,24,24,29,24,24,27}, {1,1,1,3,1,1,1,1,1,1,1,3,1,1,1,1}, {0,0,0,1,0,0,0,0,0,0,0,1,0,0,0,0}, {0,0,0,0,1,0,0,0,0,0,0,0,0,0,0,0} },
// W2: ILUVU — Donna Summer "I Feel Love"-style: the real riff isn't a
// plain octave alternation — it's a "doubles" cell (root, octave, then
// the 5th and b7th a step below the root) that gives it harmonic
// movement and a percolating, rolling feel. C3 anchors every off-beat
// (the delay-doubled note), while the low note cycles C2-C2-G1-Bb1.
{ {24,36,24,36,19,36,22,36, 24,36,24,36,19,36,22,36}, {1,1,1,1,1,1,1,1,1,1,1,1,1,1,1,1}, {0,0,0,0,0,0,0,0,0,0,0,0,0,0,0,0}, {0,0,0,0,0,0,0,0,0,0,0,0,0,0,0,0} },
// W3: CNFUSE — New Order "Confusion"-style: this is a documented
// transcription of the Pump Panel Reconstruction's 303 line (the version
// used in Blade) — G2-dominant with a drop to G1, then a section in
// A#1/A#2 (Bb), square wave, two slides and accents on steps 5/8/10/15.
{ {31,31,31,31,31,19,31,31,34,31,22,22,22,34,31,22}, {1,1,1,1,3,1,1,3,1,3,1,1,1,1,3,1}, {1,1,0,0,0,0,0,0,0,0,1,0,0,0,0,0}, {0,0,0,0,0,0,0,2,0,0,0,0,0,0,0,0} },
// W4: HISTAT — Josh Wink "Higher State of Consciousness"-style: aggressive,
// heavy accents and octave jumps with occasional glide "squeals" rather
// than glide on every other step (clearer articulation, less mushy)
{ {24,24,36,24,27,24,36,29,24,24,36,24,31,24,36,34}, {3,1,3,1,3,1,3,1,3,1,3,1,3,1,3,3}, {0,0,1,0,0,0,1,0,0,0,1,0,0,0,1,1}, {0,0,3,0,0,0,0,0,0,0,0,0,0,0,0,0} },
// W5: ACPRNC — Hardfloor "Acperience 1"-style: documented key is G major
// (was C minor). G2 anchors the riff with excursions to A2 (2nd), B2
// (3rd), D3 (5th up) and F3 (maj 7th colour tone), selective slides for
// movement, and a descending diatonic run (F3-D3-B2-A2) in the back half.
{ {31,31,31,33,35,31,31,38,31,31,33,31,41,38,35,33}, {3,1,1,1,3,1,1,1,3,1,1,1,3,1,1,1}, {0,0,1,0,0,0,0,1,0,0,1,0,0,1,1,0}, {0,0,0,0,0,0,0,0,0,4,0,0,0,0,0,0} },
// W6: SPASTK — Plastikman "Spastik"-style: tight rolling 8-step pulse with
// stutter-rests and a sudden octave-jump accent — denser than the original
// 2-hit version while keeping the minimal, glitchy character
{ {24,24,24,24,24,24,36,24, 24,24,24,24,24,24,29,24}, {1,1,0,1,1,0,3,1,1,1,0,1,1,0,3,1}, {0,0,0,0,0,0,0,0,0,0,0,0,0,0,0,0}, {0,0,0,0,0,0,3,0,0,0,0,0,0,0,3,0} },
// W7: PACIFC — 808 State "Pacific State"-style: the real bassline is a
// "snaking 16th-note" SH-101 line in D minor with octave jumps giving it
// "syncopated funk" (the original was C-major arpeggiated, wrong key and
// too smooth). D2 is the anchor, with octave jumps to D3 and movement
// through the D minor triad (D-F-A) plus the G passing tone.
{ {26,26,38,29,26,33,29,26,26,38,31,29,26,33,31,29}, {3,1,1,3,1,1,1,3,3,1,1,3,1,1,1,3}, {0,1,0,0,1,0,1,0,0,1,0,0,1,0,1,0}, {0,0,0,0,0,0,0,0,0,0,0,0,0,5,0,0} },
};
const char* VSTRIP_WALKS[NUM_WALKS] = {"DAFNK","ACIDTR","ILUVU","CNFUSE","HISTAT","ACPRNC","SPASTK","PACIFC"};
// Full names shown in the CUT/RES label area when a walk is active
const char* WALK_FULLNAMES[NUM_WALKS] = {"DA FUNK","ACID TRACKS","I FEEL LOVE","CONFUSION","HIGHER STATE","ACPERIENCE 1","SPASTIK","PACIFIC STATE"};
// Tempos matching each track (BPM)
const uint16_t WALK_TEMPOS[NUM_WALKS] = {111, 120, 125, 134, 130, 125, 126, 125};
// Pattern lengths (steps) — shorter, tighter loops for tracks built on
// hypnotic repeating cells (Da Funk, Acid Tracks, I Feel Love, Spastik),
// full 16 for tracks with a longer evolving phrase (Confusion, Higher
// State, Acperience 1, Pacific State)
const uint8_t  WALK_LENS[NUM_WALKS]   = {16, 8, 8, 16, 16, 16, 8, 16};
// Sound engine per track — chosen for tonal character:
//   0=SAW+LPF (classic acid), 1=SQR+LPF (hollow/punchy), 2=SINE+LPF (smooth),
//   4=CSAW+COMB (metallic/ringing resonance)
const uint8_t  WALK_SOUNDS[NUM_WALKS] = {1, 0, 1, 1, 0, 0, 1, 1};

// Default pattern: C2 C2 C2 Eb2 C2 C3 G2 F2 C2 G2 F2 G2 C3 C2 C3 Eb3
// (key=0, scale=CHROM, octave=1 — absolute semitones)
Sequencer seq = {
  {
    {24,true,false,false,0},{24,true,false,false,0},
    {24,true,false,false,0},{27,true,false,false,0},
    {24,true,false,false,0},{36,true,false,false,0},
    {31,true,false,false,0},{29,true,false,false,0},
    {24,true,false,false,0},{31,true,false,false,0},
    {29,true,false,false,0},{31,true,false,false,0},
    {36,true,false,false,0},{24,true,false,false,0},
    {36,true,false,false,0},{39,true,false,false,0},
  },
  {24,24,24,27,24,36,31,29,24,31,29,31,36,24,36,39},  // origNote working copy
  {24,24,24,27,24,36,31,29,24,31,29,31,36,24,36,39},  // rootNote permanent (key=C)
  0,16,false,120,0,0,1,0,0,0,0,0,0
};

// =====================================================================
// PATCH SAVE / LOAD  (EEPROM emulated in RP2040 flash)
// =====================================================================
#define NUM_SLOTS   4
#define EEPROM_SIZE 1064  // was 1024 — bumped again to reserve 40 fresh bytes at
                          // the tail (addresses 1024-1063) for the CUSTOM drum
                          // pattern's own persisted slot. See BM_CUSTOM_ADDR in
                          // BeatMachine2.ino — placed right at the old 1024
                          // boundary since everything below 1024 is already
                          // claimed (SLOT/ACCENT/CH2/CH2_SLOT/CH2_EUC/MIX). RP2040
                          // EEPROM emulation reserves a full flash sector
                          // regardless of the size requested here, so this is free.
#define PATCH_VALID 0xAC   // magic byte — slot has valid data
// Whether acid was playing when this slot was saved, packed into the spare
// top bit of p.rrMode (rrMode only ever uses values 0-7, bits 0-2 — see
// constrain() in loadPatch()). Deliberately NOT a new struct field: Patch
// contains a uint16_t (tempo), so appending a field grows sizeof(Patch) by
// 2 bytes (alignment padding), not 1 — which cascades forward through the
// macro-computed ACCENT_ADDR/CH2_ADDR chain and lands CH2_ADDR exactly on
// BM_EEPROM_BASE (256). Confirmed by hand: PATCH_SIZE 60->62 pushes
// CH2_ADDR from 248 to 256. See the BmPatch comment below for the same
// class of collision already hit once and reverted — not repeating it here.
#define PATCH_PLAYING_BIT 0x08

struct Patch {
  uint8_t valid;
  uint8_t note[NUM_STEPS];
  uint8_t flags[NUM_STEPS];  // bit0=active, bit1=accent, bit2=glide
  uint8_t effect[NUM_STEPS];
  uint8_t key, scale, sound, octave, len; int8_t trans; uint8_t algo;
  uint16_t tempo;
  uint8_t kwMode, rrMode;  // rrMode (PAT> playback order) — reuses the byte formerly named swingAmt
};
#define PATCH_SIZE   ((int)sizeof(Patch))
#define SLOT_ADDR(s) ((s) * PATCH_SIZE)

// Accent envelope settings — stored in their own slot, just past the 4
// pattern slots, so they persist independently of pattern saves/loads.
#define ACCENT_VALID   0xAE   // magic byte — accent settings slot has valid data
#define ACCENT_ADDR    (NUM_SLOTS * PATCH_SIZE)
struct AccentSettings {
  uint8_t valid;
  int16_t envCutoff;  // 0-255
  int16_t envRes;     // 0-400
  int16_t decayDiv;   // 1-10
};
#define ACCENT_SETTINGS_SIZE ((int)sizeof(AccentSettings))

// Channel 2 tuning — own slot just past the accent settings, same reasoning:
// persists independently of pattern saves/loads and of accent tuning.
// Magic byte bumped 0xC2->0xC3: struct gained `sound`, so an old slot from
// before the multi-engine update is correctly treated as "no saved data"
// rather than being misread.
#define CH2_VALID   0xC3
#define CH2_ADDR    (ACCENT_ADDR + ACCENT_SETTINGS_SIZE)
struct Ch2Settings {
  uint8_t valid;
  int8_t  octave;       // -2..+2
  int16_t detuneCents;  // 0-50
  uint8_t wave;         // legacy — superseded by `sound`, kept so old field layout math stays obvious
  uint8_t sound;        // 0-7, selects ch2 synth engine — see CH2_SND_NAMES
  uint8_t amount;       // 0-255, generic live "character" knob (was the DCY-pot wave toggle)
};
#define CH2_SETTINGS_SIZE ((int)sizeof(Ch2Settings))

// CH2 settings v2 — EXTENDED blob, relocated to the tail of EEPROM.
// WHY RELOCATED: the original Ch2Settings at CH2_ADDR (248) ends at byte
// 256 — EXACTLY where BM_EEPROM_BASE starts the four drum patch slots.
// Zero headroom: growing the old struct in place would corrupt drum
// slot 1's valid byte. Drum slots span 256..399 (4 x 36), so this blob
// lives at 400 with 112 bytes of room. The legacy 248 blob is read ONCE
// as a migration source (see loadCh2Settings) and is otherwise dead
// space — do NOT reuse it for anything else.
#define CH2X_VALID  0xCC   // bumped 0xCB->0xCC: struct gained `playing` (play
                           // state on save). Confirmed by hand this doesn't
                           // change sizeof(Ch2SettingsX) — it lands in
                           // pre-existing tail alignment padding (still 78
                           // bytes) — but the byte there in OLD saves is
                           // whatever uninitialized padding happened to be
                           // in RAM at save time, not a safe false default,
                           // so old blobs must still be treated as invalid.
#define CH2X_ADDR   400
struct Ch2SettingsX {
  uint8_t  valid;        // CH2X_VALID
  int8_t   octave;       // -2..+2
  int16_t  detuneCents;  // 0-50
  uint8_t  sound;        // 0-7 engine (legacy `wave` dropped — superseded)
  uint8_t  amount;       // 0-255 per-engine character
  uint8_t  pitchMode;    // 0-7: OFF,INV,RNDH,CHRD,FOLW,PDL,ECH1,WALK
  uint8_t  decaySel;     // 0-7 index into CH2_ENVM
  uint16_t steps;        // ch2Steps[] bitmap, bit i = step i — the pattern
                         // itself now survives power cycles
  uint8_t  echoSel;      // reserved (round 2) — 0 = OFF
  uint8_t  verbSel;      // reserved (round 2) — 0 = OFF
  uint8_t  autoRec;         // REC: bit L set = lane L has a pot-motion recording
  int8_t   stepNote[16];    // NOTE per-step pitch: chord-tone interval, 127 = none
  uint8_t  autoVal[3][16];  // REC: recorded raw>>2 per lane (OCT/AMT/DCY) per step
  uint8_t  playing;         // driftPlaying at save time — lands in what was
                             // trailing alignment padding, confirmed by hand
                             // (struct stays 78 bytes). See CH2X_VALID bump.
};
#define CH2X_SETTINGS_SIZE ((int)sizeof(Ch2SettingsX))
static_assert(sizeof(Ch2SettingsX) == 78, "Ch2SettingsX size changed — recheck 400+size <= 512");
static_assert(CH2X_ADDR + sizeof(Ch2SettingsX) <= 512, "Ch2SettingsX overruns EEPROM");

bool     slotHasData[4]  = {false,false,false,false};
int8_t   lastLoadedSlot  = -1;   // -1 = none loaded this session
volatile bool saveCommit = false;
uint8_t  saveSlotPending = 255;
uint32_t saveSlotDownMs  = 0;
#define  SAVE_HOLD_MS 1000

// Per-slot DRIFT (channel 2) storage — same Ch2SettingsX layout as the
// single always-on CH2X blob above, but one copy per numbered slot (0-3),
// living well past everything else now that EEPROM_SIZE is 1024. This is
// what makes save/load "combined": acid (SLOT_ADDR), drums (BM_SLOT_ADDR,
// in BeatMachine2.ino) and DRIFT (here) all get their own region indexed
// by the same slot number, and saveAllToSlot()/loadAllFromSlot() below
// touch all three together regardless of which screen you triggered the
// save/load gesture from.
#define CH2_SLOT_VALID   CH2X_VALID
#define CH2_SLOT_BASE    512
#define CH2_SLOT_ADDR(s) (CH2_SLOT_BASE + (s) * (int)sizeof(Ch2SettingsX))
static_assert(CH2_SLOT_BASE + 4 * (int)sizeof(Ch2SettingsX) <= EEPROM_SIZE, "ch2 slot region overruns EEPROM");
bool     ch2SlotHasData[4] = {false,false,false,false};

// PATT — user-savable custom pattern slots for the DRIFT PATT page
// (S1..S8 tiles). Originally this was EUC, a fixed floor-euclidean fill
// E(k,16), k = tile+1 — good for E5-E8 (5-8 pulses/16), rarely useful for
// E1-E4 (1-4 pulses is a pretty narrow creative space). The fixed fills are
// gone entirely now: all 8 slots start BLANK, long-holding a tile SAVES
// whatever is currently painted into ch2Steps as that slot's pattern, and
// a plain tap LOADS it back (blank if nothing's been saved there yet).
// Lives in the unused gap between the CH2_SLOT region (ends 824) and
// MIX_ADDR (900) — see the address map above.
#define CH2_EUC_VALID 0xE1
#define CH2_EUC_ADDR  824
struct Ch2EucSlots {
  uint8_t  valid;
  uint8_t  savedMask;   // bit i set = slot i holds a saved custom pattern
  uint16_t steps[8];    // custom pattern per slot (bit i = step i), valid
                         // only where savedMask's matching bit is set
};
#define CH2_EUC_SLOTS_SIZE ((int)sizeof(Ch2EucSlots))
static_assert(CH2_EUC_ADDR + sizeof(Ch2EucSlots) <= 900, "Ch2EucSlots overruns MIX_ADDR");
uint8_t  ch2EucSavedMask       = 0;        // RAM mirror of Ch2EucSlots.savedMask
uint16_t ch2EucCustom[8]       = {0};      // RAM mirror of Ch2EucSlots.steps[]

// MIX SETTINGS — per-engine output trim (acid/DRIFT/drums), tuned via
// MIX EDIT (hold pads 15+16), same slot-independent persistence pattern
// as accent settings used to be: one global value, not per-numbered-slot.
// Bumped 0xC7 -> 0xC8: acid unity moved from 255 to MIX_UNITY (170), so a
// saved acidLevel of 255 now means +1.5x boost rather than "normal". Old
// saves would load as a blaring acid channel; a new magic byte makes them
// fail validation and fall back to the (now symmetric) defaults instead.
#define MIX_VALID  0xC8
#define MIX_ADDR   900
struct MixSettings {
  uint8_t valid;
  uint8_t acidLevel;
  uint8_t driftLevel;
  uint8_t drumLevel;
};
#define MIX_SETTINGS_SIZE ((int)sizeof(MixSettings))
static_assert(MIX_ADDR + sizeof(MixSettings) <= EEPROM_SIZE, "MixSettings overruns EEPROM");

// FILTER SETTINGS — the runtime filter params tuned via SETTINGS mode (hold
// pads 1+2+3). Lands in the fresh reserved bytes past MIX_ADDR. Magic byte so
// an un-initialised EEPROM (or an older build) falls back to the SEED defaults.
#define FILTER_VALID 0xF3
#define FILTER_ADDR  1024
struct FilterSettings {
  uint8_t valid;
  int16_t envCut;    // gEnvCutNorm  (0-255)
  int16_t decayDiv;  // gEnvDecayDiv (2-20)
  int16_t cutMax;    // gHpCutMax  (110-190; was slopeB pre-0xF3)
};
static_assert(FILTER_ADDR + sizeof(FilterSettings) <= EEPROM_SIZE, "FilterSettings overruns EEPROM");

// =====================================================================
// UI / MENU
// =====================================================================
enum FuncSel {
  FUNC_NONE=-1,
  FUNC_KEY=0, FUNC_PAT, FUNC_SOUND, FUNC_WALK, FUNC_FX, FUNC_TEMPO, FUNC_PLEN, FUNC_PATMODE
};

const char* SNAMES[] = {
  "SAW+LPF","SQUARE+LPF","SINE+LPF","NOISE+LPF",
  "SAW+COMB","SQUARE+COMB","SINE+COMB","NOISE+COMB",
  "PULSE LFO","MULTI SQUARE","WAVESHAPE"
};

// Indices 8-11 are legacy entries unreachable from the UI
const char* FXNAMES[] = {
  "None","Oct Up","Retrigger","Stutter",
  "Maj Step","Min Step","Dom7 Step","Dim Step",
  "Compressor","Overdrive","Sine Modulate","Bit Crush"
};

const char* NNAMES[]    = {"C","C#","D","D#","E","F","F#","G","G#","A","A#","B"};
const char* SCNAMES[]   = {"CHROMATIC","MAJOR","MINOR","PENTATONIC","BLUES"};
const char* FUNCNAMES[] = {"KEY","RIFF","SOUND","WALK","FX","TEMPO","PLEN","PAT>"};

// =====================================================================
// KEY WALK
// =====================================================================
// kwMode: 0=off
//   1=4TH     root(2 bars) -> +4th(2 bars) -> repeat
//   2=OCTWAVE call & response: root(2 bars) -> +12 accented(2 bars) -> root glided(2 bars) -> repeat
//   3=5TH     root(2 bars) -> +5th(2 bars) -> repeat
//   4=BOUNCE  root(2 bars) -> +2nd(2 bars) -> repeat
//   5=MIN3RD  root(2 bars) -> +b3(2 bars) -> repeat
//   6=VAMP3   root(2 bars) -> +5th(2 bars) -> +4th(2 bars) -> repeat (6-bar cycle)
//   7=RND1    random musical destination each 2 bars
uint8_t  kwMode      = 0;
uint8_t  kwStepCount = 0;
uint8_t  kwEventCount= 0;
int8_t   kwRoot      = 0;
int8_t   kwOctTrans  = 0;   // OCTWAVE: current trans offset (0 or +12)
bool     kwForceAccent = false;  // OCTWAVE: force accent on the octave-hit step
bool     kwForceGlide  = false;  // OCTWAVE: force glide on the return-to-root step

const char* KWNAMES[] = {
  "OFF","4TH","OCTWAVE","5TH",
  "BOUNCE","MIN3RD","VAMP3","RANDOM"
};

// Value strip tile labels (max 5 chars)
const char* VSTRIP_KEY[8] = {"C","D","Eb","F","G","Ab","Bb","B"};
const char* VSTRIP_PAT[8] = {"DFLT","SQNCE","FUNK","MINI","JUMP","RAVE","SYNC","DARK"};
const char* VSTRIP_OCT[8] = {"CHROM","MAJ","MIN","PENT","BLUES","OCT0","OCT1","OCT2"};
const char* VSTRIP_SND[8] = {"SAW","SQR","SINE","PWM","CSAW","CSQR","CSIN","SUBSQ"};
const char* VSTRIP_WLK[8] = {"OFF","4TH","OCTWV","5TH","BNCE","MIN3","VAMP3","RND"};
const char* VSTRIP_FX[8]  = {"NONE","OCT+","RTRG","STUT","MSTP","mSTP","D7ST","DMST"};
const char* VSTRIP_PLN[8] = {"1","2","3","4","6","8","12","16"};
const char* VSTRIP_PMD[8] = {"FWD","CW","ALT","REV","SKIP2","SKIP3","PING","RND"};

const uint16_t TEMPO_PRESETS[8] = {100,110,120,128,133,138,145,160};
const char*    VSTRIP_BPM[8]    = {"100","110","120","128","133","138","145","160"};

// =====================================================================
// SCALES
// =====================================================================
const uint8_t SCALE_CHROMATIC[] = {0,1,2,3,4,5,6,7,8,9,10,11};
const uint8_t SCALE_MAJOR[]     = {0,2,4,5,7,9,11};
const uint8_t SCALE_MINOR[]     = {0,2,3,5,7,8,10};
const uint8_t SCALE_PENTA[]     = {0,2,4,7,9};
const uint8_t SCALE_BLUES[]     = {0,3,5,6,7,10};

const uint8_t* SCALES[]    = {SCALE_CHROMATIC,SCALE_MAJOR,SCALE_MINOR,SCALE_PENTA,SCALE_BLUES};
const uint8_t  SCALE_LENS[]= {12,7,7,5,6};
#define SCALE_OCTS 3

uint8_t scalePosCount() { return SCALE_LENS[seq.scale] * SCALE_OCTS; }

// scaleNote(stepIdx): maps origNote through current scale using chromatic degree-index mapping.
// origNote is never mutated — switching back to CHROM restores the exact original pitch.
uint8_t scaleNote(uint8_t stepIdx) {
  uint8_t raw = seq.origNote[constrain((int)stepIdx, 0, NUM_STEPS-1)];
  if (seq.scale == 0) return constrain((int)raw, 0, 59);

  int base = (int)seq.key + (int)seq.octave * 12;
  int rel  = (int)raw - base;
  int reg  = rel / 12;
  int pc   = rel % 12;
  if (pc < 0) { pc += 12; reg--; }
  reg = constrain(reg, 0, 2);

  uint8_t to_len = SCALE_LENS[seq.scale];
  uint8_t mapped = (uint8_t)(((uint16_t)pc * to_len + 6) / 12);
  if (mapped >= to_len) mapped = to_len - 1;

  int result = (int)seq.key + (int)SCALES[seq.scale][mapped]
               + reg * 12 + (int)seq.octave * 12;
  return (uint8_t)constrain(result, 0, 59);
}

// Convert scale position index to absolute semitone
uint8_t scalePosToAbs(uint8_t pos) {
  uint8_t len = SCALE_LENS[seq.scale];
  uint8_t oct = pos / len;
  uint8_t deg = pos % len;
  int n = (int)seq.key + (int)SCALES[seq.scale][deg] + (int)oct*12 + (int)seq.octave*12;
  return (uint8_t)constrain(n, 0, 59);
}

// Snap cache: rawNote (0-59) → nearest scale position index (for CUT-pot note editor)
uint8_t snapCache[60];
bool    snapCacheDirty = true;

void rebuildSnapCache() {
  uint8_t total = scalePosCount();
  for (uint8_t n = 0; n < 60; n++) {
    uint8_t best = 0; int bestDist = 9999;
    for (uint8_t p = 0; p < total; p++) {
      int d = abs((int)scalePosToAbs(p) - (int)n);
      if (d < bestDist) { bestDist = d; best = p; }
    }
    snapCache[n] = best;
  }
  snapCacheDirty = false;
}

uint8_t snapToScale(uint8_t rawNote) {
  if (snapCacheDirty) rebuildSnapCache();
  return snapCache[constrain((int)rawNote, 0, 59)];
}

// Snap absolute semitone to nearest note in current scale
uint8_t snapAbsToScale(uint8_t absNote) {
  uint8_t total = scalePosCount();
  uint8_t bestNote = absNote; int bestDist = 9999;
  for (uint8_t p = 0; p < total; p++) {
    uint8_t candidate = scalePosToAbs(p);
    int d = abs((int)candidate - (int)absNote);
    if (d < bestDist) { bestDist = d; bestNote = candidate; }
  }
  return bestNote;
}

// =====================================================================
// UI STATE
// =====================================================================
struct UI {
  uint8_t  editStep;
  bool     dirty;
  bool     fullDirty;
  bool     editDirty;
  bool     funcDirty;
  bool     cellsDirty;
  bool     barDirty;
  bool     valDirty;
  bool     infoDirty;
  uint8_t  cellIdx;
  uint32_t lastMs;
  // Save/load overlay
  bool     slotOverlay;       // true = show save/load banner
  uint8_t  slotOverlaySlot;   // slot number 0-3
  bool     slotOverlaySave;   // true=save, false=load
  bool     slotOverlayEmpty;  // true=load of empty slot
  bool     slotOverlayCleared;// true=show "ACID SLOTS CLEARED" banner (core1-rendered)
  uint32_t slotOverlayMs;     // millis() when overlay was triggered
  uint8_t  slotProgress;      // 0-100, fill % during hold-to-save
  bool     slotProgressShow;  // true = show progress bar (holding)
};
UI ui = {0,true,true,false,false,false,false,false,false,0,0,
         false,0,false,false,false,0,0,false};

void loadPreset(uint8_t idx) {
  if (idx >= NUM_PRESETS) return;
  curPreset = idx;
  const PresetPattern& p = PRESETS[idx];
  seq.key = 0;  // presets stored in key=C; reset key so rootNote == origNote
  for (uint8_t i = 0; i < NUM_STEPS; i++) {
    seq.steps[i].note   = p.note[i];
    seq.rootNote[i]     = p.note[i];   // permanent C-relative store
    seq.origNote[i]     = p.note[i];   // working copy (same as root since key=C)
    seq.steps[i].active = p.flags[i] & 1;
    seq.steps[i].accent = (p.flags[i] >> 1) & 1;
    seq.steps[i].glide  = p.glide[i];
    seq.steps[i].effect = p.effect[i];
  }
  seq.len = 16;
  ui.dirty=true; ui.fullDirty=true; ui.cellsDirty=true; ui.cellIdx=0; ui.infoDirty=true;
}

// EASTER EGG: load one of the 8 Acid Walks patterns (same layout as loadPreset)
void loadWalk(uint8_t idx) {
  if (idx >= NUM_WALKS) return;
  curWalk = idx;
  const PresetPattern& p = WALK_PATTERNS[idx];
  seq.key = 0;
  for (uint8_t i = 0; i < NUM_STEPS; i++) {
    seq.steps[i].note   = p.note[i];
    seq.rootNote[i]     = p.note[i];
    seq.origNote[i]     = p.note[i];
    seq.steps[i].active = p.flags[i] & 1;
    seq.steps[i].accent = (p.flags[i] >> 1) & 1;
    seq.steps[i].glide  = p.glide[i];
    seq.steps[i].effect = p.effect[i];
  }
  seq.len = WALK_LENS[idx];
  if (seq.cur >= seq.len) seq.cur = 0;
  seq.tempo    = WALK_TEMPOS[idx];
  seq.interval = bpm2us(seq.tempo);
  seq.sound    = WALK_SOUNDS[idx];
  noInterrupts();
  gSound     = seq.sound;
  filtA = filtB = 0; filtA2 = filtB2 = 0; HA1 = HB1 = HA2 = HB2 = 0;
  gEnvCutoff = 0;
  gEnvRes    = 0;
  interrupts();
  ui.dirty=true; ui.fullDirty=true; ui.cellsDirty=true; ui.cellIdx=0; ui.infoDirty=true; ui.valDirty=true; ui.barDirty=true;
}

// =====================================================================
// BUTTON STATE
// =====================================================================
#define DB        20
#define LG       500    // long-press threshold (ms)
#define RPT_DELAY 300
#define RPT_RATE   80

bool     pState[16]={false}, pLast[16]={false}, pLong[16]={false};
uint32_t pDeb[16]={0}, pDown[16]={0};
uint8_t  pCycle[16]={0};
bool     pNoteEdit[16]={false};
uint8_t  pLastPotStep[16]={255};
bool     pChord[16]={false};

bool     funcMode = false;
FuncSel  funcSel  = FUNC_NONE;

uint32_t tapLastMs = 0;
uint8_t  tapCount  = 0;
uint32_t tapSumMs  = 0;
#define  TAP_TIMEOUT 2000

bool    fxAssignMode  = false;
bool    fxAssignHasFx = false;
bool    fxAssignFresh = false;
uint8_t fxAssignFx    = 0;

// PATMODE: 0=fwd 1=fwd1-8 2=fwd9-16 3=rev 4=rev1-8 5=rev9-16 6=pingpong 7=random
uint8_t rrMode    = 0;
bool    rrPingFwd = true;

bool     syncIn=false, syncOk=false;
bool     syncMode=false;     // true = sync active this boot (either direction) —
                              // pad 14 held at power-on. GP2 is repurposed away
                              // from drum/DRIFT audio either way.
bool     syncOutMode=false;  // direction, valid only when syncMode is true:
                              // false = SYNC IN (GP2 listens for an external
                              // clock, unchanged from V4/V5). true = SYNC OUT
                              // (GP2 generates a DIN-sync-style clock from this
                              // device's own tempo) — pads 14+13 held together
                              // at power-on. See setup()'s BOOT MODE DETECT.
// ── SYNC CLOCK MODEL: DIRECT ──────────────────────────────────────────
// Matches the rest of the synth ecosystem (Freaq / Bass_Synth / Medusa):
// SYNC OUT emits one clean digital gate per step (digitalWrite HIGH, pulled
// LOW after a fixed width); SYNC IN advances the sequencer directly, one step
// per incoming pulse — no tempo measurement, no PPQN-per-quarter math.
//
// The previous model was PWM/PPQN-based: it drove GP2 with analogWrite() as a
// pulse *train* and derived tempo by measuring pulse intervals. At a low pulse
// rate the audio-rate PWM carrier reads as a steady DC-ish voltage, not a gate
// (the "constant output, not a pulse" symptom), and the tempo-derivation never
// lined up with per-step-clocked gear. Both are replaced below.
#define  SYNC_STEPS_PER_PULSE  4    // Sequencer 16th-note steps per sync pulse.
                                     // Your gear clocks 1 pulse per BEAT and acid
                                     // sequences 16ths (4 per beat), so 1 pulse =
                                     // 4 steps: SYNC IN subdivides each pulse into
                                     // 4 evenly-timed steps at the measured tempo;
                                     // SYNC OUT emits 1 gate every 4 steps. Set 1
                                     // for a per-16th-step clock, 2 for per-8th.
#define  SYNC_OUT_PULSE_MS     15   // SYNC OUT: gate width per step, in ms. GP2
                                     // goes HIGH on each step and is pulled LOW
                                     // this long after — a genuine digital gate
                                     // (digitalWrite), same as every synth here.
uint32_t syncOutPulseOffMs = 0;      // millis() at which to pull the sync-out gate
                                     // low; 0 = idle (line held low).
uint8_t  syncOutStepCtr    = 0;      // steps since the last sync-out gate — emits
                                     // one gate every SYNC_STEPS_PER_PULSE steps.

// ── DRIFT OUTPUT ──────────────────────────────────────────────────────
// Settled behavior: ACID lives on GP15 (this file's updateAudio()), alone,
// always — same as the very first single-voice design. DRIFT lives on GP2
// instead (BeatMachine2.ino's bmFillDrumBufferTo()), additively summed with
// drums there. GP15 and GP2 meet at a shared analog audio node on the PCB,
// blended by a PHYSICAL mix pot — that pot, not any ratio in software, is
// the real-time acid/DRIFT balance control, and it's continuously
// variable rather than a fixed constant. Pads 9+10+11 swap ch2SynthMode,
// which decides which one the pad/pot SURFACE currently edits — it has no
// bearing on which is audible or on the mix balance; that's the physical
// pot's job, not this flag's.
//
// (An earlier attempt summed DRIFT digitally into THIS function instead,
// putting both engines on GP15 together at a fixed software ratio. That
// technically made them simultaneously audible, but left the physical mix
// pot with nothing to blend — it can only act on GP15 vs GP2, and once
// DRIFT was already summed into GP15 in software, there was no longer a
// separate DRIFT signal on GP2 for the pot to bring in or take away.)
//
// Drums stay additively summed with DRIFT on GP2 (not a separate output),
// so drums are present whenever the pot includes any GP2 in the blend,
// regardless of whether DRIFT itself is currently playing.

// CHANNEL 2 "DRIFT" (second synth voice) — RUNTIME-selected: hold pads
// 9+10+11 for 1s (the layer chord; 9+10 alone is drums). The old
// pad-11-at-boot selection is gone.
// ch2SynthMode means "DRIFT is the current EDIT FOCUS" — which screen is
// showing, which pads/pots are wired to which engine's parameters. It does
// NOT mean "DRIFT is audible" — that's acid's/DRIFT's own play flags
// (below) plus the physical mix pot, entirely independent of which one
// ch2SynthMode currently points at. Toggling it swaps which of
// acidPlaying/driftPlaying the pads-1+2 chord controls, but leaves the
// OTHER one's play state (and audibility) completely untouched.
volatile bool ch2SynthMode = false;  // RUNTIME edit-focus selection
                                     // (volatile: core 0 flips it
                                     // mid-session, core 1's fill loop
                                     // reads it too). No longer a boot-time
                                     // flag — selected by the 9+10(+11)
                                     // layer chord.

// seqIsRunningForDisplay(): "is the shared step position walking" from
// the perspective of the playhead cursor and DRIFT's live-play gestures
// (KBRD transpose, quantized note-record) — a UI-display question, about
// whichever engine's screen is currently showing (ch2SynthMode), NOT about
// audio mixing (that's the physical mix pot's job, independent of this
// flag). NOT the same question as seq.running, which also has to account
// for drums (bmPlaying) and BOTH engines regardless of which is on screen.
// Whichever of acid/DRIFT is currently the edit focus (ch2SynthMode) is
// the one whose own play flag answers this — the other one's flag may
// still be true (and audible, if the pot includes its output) but isn't
// what's walking the cursor on the screen you're looking at right now.
bool seqIsRunningForDisplay() {
  return ch2SynthMode ? driftPlaying : acidPlaying;
}

bool     ch2EditMode    = false;  // viewing/editing channel 2: pads toggle ch2Steps[],
                                    // CUT/RES/DCY live-control octave/detune/amount
#define LAYER_PAD_C 10            // pad 11 — the DRIFT selector in the layer chord
bool     p11Deferred    = false;  // pad 11 pressed while 9/10 held — action
                                  // deferred to release (chord may be forming)
bool     layerArmed     = false;  // pads 9+10 landed; waiting out LAYER_HOLD_MS
                                  // before firing, so pad 11 has time to land too
uint32_t layerArmMs = 0;
#define  LAYER_HOLD_MS 500        // short hold, NOT an accidental-trigger guard —
                                  // it exists purely to give pad 11 a window to
                                  // arrive after 9/10 without the chord already
                                  // having fired as DRUMS

// SECOND-LAYER chord (pads 9+10, optionally +11). Arms the instant 9+10
// complete, then fires after LAYER_HOLD_MS. WHICH engine is decided AT
// FIRE TIME by whether pad 11 is also down: 9+10 = DRUMS, 9+10+11 =
// DRIFT (channel 2) — EXCEPT from inside drums itself, where 9+10+11 is
// a deliberate no-op (see the bmMode check below). Called from both this
// file's and BeatMachine2.ino's pad scans (one translation unit) so
// either mode can trigger it identically.
void fireLayerChord() {
  bool wantDrift = (digitalRead(PAD_PINS[LAYER_PAD_C]) == LOW);
  if (wantDrift && bmMode) {
    // 9+10+11 pressed WHILE IN DRUMS — no-op, deliberately. This chord's
    // job while in drums is just the 9+10 exit-to-acid gesture; adding
    // pad 11 into that mix was jumping straight to DRIFT, which made it
    // too easy to land in the wrong place with an imprecise 3-pad press.
    // Pad 11 was chord fuel here too: eat its press (bmPChord[10]) so its
    // eventual release doesn't fall through to the deferred beat-select
    // replay (see BeatMachine2.ino's pad-scan release handler) and select
    // a pattern nobody asked for — the "PACIFIC ST turns on" symptom this
    // fixes. pChord[LAYER_PAD_C] (the ACID-side array) stays untouched;
    // it's irrelevant here since acid's own pad scan doesn't run while
    // bmMode is true.
    bmPChord[10] = true; bmP11Deferred = false;
    return;
  }
  if (wantDrift) {
    // 9+10+11 — toggle DRIFT on/off, i.e. swap which of acid/DRIFT is the
    // CURRENT EDIT FOCUS (ch2SynthMode) — which one the pad/pot surface
    // controls. This does NOT swap which is audible: acid and DRIFT can
    // both be playing and both be in the mix (blended by the PCB's
    // physical mix pot) regardless of ch2SynthMode — see the DRIFT
    // OUTPUT comment near ch2SynthMode's declaration.
    // Each engine's own play/stop state (acidPlaying / driftPlaying) is
    // untouched by this — swapping edit focus is a different action from
    // starting/stopping one (pads 1+2).
    // Pad 11 was chord fuel: eat its release and clear any pre-chord
    // residue (a note-edit it may have opened before 9/10 landed).
    pChord[LAYER_PAD_C]=true; p11Deferred=false;
    pCycle[LAYER_PAD_C]=0; pNoteEdit[LAYER_PAD_C]=false; pLastPotStep[LAYER_PAD_C]=255;
    if (!ch2SynthMode) {
      // Turning DRIFT the EDIT FOCUS — GP2 hardware is already running
      // from boot (see setup()), so there's nothing to start here; this
      // only ever changes which engine the pads/pots control, never
      // audio routing.
      ch2SynthMode = true;
      ch2EditMode  = true;
    } else {
      // DRIFT -> ACID: persist DRIFT, drop back to the acid voice/screen.
      if (ch2EditMode) saveCh2Settings();
      ch2SynthMode = false;
      ch2EditMode  = false;
    }
    ui.dirty=true; ui.fullDirty=true; ui.barDirty=true; ui.infoDirty=true;
  } else {
    // 9+10 — DRUMS. doModeSwitch() just toggles bmMode; entering or
    // leaving is never refused (drums additively share GP2 with DRIFT,
    // never displacing it, and don't touch acid on GP15 at all).
    doModeSwitch();   // sets its own dirty flags / FIFO redraw
  }
}
// Sound-engine selection lives on the CH2 FUNC page (SND, slot 1) while
// ch2EditMode is on — ch1's FUNC_SOUND is ch1's in every mode (the old
// ch2SynthMode hijack of FUNC+11 is gone). CH2 EDIT itself (this
// hold-chord) stays a plain STEP-only toggle for ch2Steps[], and yields
// to funcMode so the two don't fight over the same pads (see the
// ch2EditMode press/release branches).
bool     ch2Steps[NUM_STEPS]  = {false}; // on/off per step — the rhythmic pulse layer
// NOTE: per-step pitch for DRIFT, recorded live. Value is a CHORD-TONE
// INTERVAL INDEX (0..CH2_KB_KEYS-1 — ROOT/3RD/5TH/OCT/2ND/4TH/7TH/-OCT,
// see ch2KbIntervalSemis), so a recorded step tracks key AND chord
// changes, not a fixed pitch. Sentinel 127 = "no recorded note, follow
// the PITCH mode" (the default for every step, so existing patterns and
// ARP/WALK are unchanged). Tapping a NOTE key plays it immediately AND,
// if the sequencer is running, records it onto the step under the
// playhead — so playing a few notes builds a loop that repeats on its
// own from then on.
#define CH2_STEP_NONE 127
int8_t   ch2StepNote[NUM_STEPS] = { CH2_STEP_NONE,CH2_STEP_NONE,CH2_STEP_NONE,CH2_STEP_NONE,
                             CH2_STEP_NONE,CH2_STEP_NONE,CH2_STEP_NONE,CH2_STEP_NONE,
                             CH2_STEP_NONE,CH2_STEP_NONE,CH2_STEP_NONE,CH2_STEP_NONE,
                             CH2_STEP_NONE,CH2_STEP_NONE,CH2_STEP_NONE,CH2_STEP_NONE };
// DRIFT is hard-locked to exactly 16 steps by TWO things: the 16 physical
// pads map 1:1 to steps (see the ch2Steps toggle in the pad handlers), and
// ch2Steps is persisted as a uint16_t bitmap (Ch2SettingsX.steps). Bumping
// NUM_STEPS above 16 would silently drop high steps on save and leave them
// unreachable from the pads; below 16 would leave pads pointing past the
// arrays. Widening DRIFT needs a pad remap AND a wider save format — until
// then this assert turns "someday" memory/data corruption into a build error.
static_assert(NUM_STEPS == 16, "DRIFT step count is locked to 16: 16 pads map 1:1 to steps and ch2Steps saves as a uint16_t bitmap.");
#define CH2_KB_KEYS   8           // top-row pads = 8 chord-tone intervals
int16_t  ch2KbNoteOverride = -1;  // >=0: a live NOTE press, exact note for the
                                  // next triggerCh2Pulse; -1 = normal (core0 only)
int8_t   ch2Octave      = -1;     // -2..+2 octaves relative to channel 1's root key, via CUT pot (live)
uint16_t ch2EnvMLive = 0;         // live per-sample decay multiplier from pot 3
                                  // (0 = not yet set; triggerCh2Pulse falls back)
uint16_t ch2DcyDisplay = 512;     // raw DCY pot (0-1023) for the DRIFT bar fill
uint16_t ch2OctDisplay = 512;     // raw OCT pot (0-1023) — bar tracks the VALUE
uint16_t ch2AmtDisplay = 512;     // raw AMT pot (0-1023)   driving the sound, so
                                  // recorded automation animates the bar and a
                                  // turned-but-recorded pot does NOT move it
int16_t  ch2DetuneCents = 18;     // 0-30 cents, LIVE on RES pot for DTSQR/UNISN only — was the
                                    // this; UNISN uses it to space its second voice off the first
uint8_t  ch2Wave         = 0;     // legacy 0/1 sub-sine/detuned-square toggle — superseded by ch2Sound,
                                    // kept only so old boards mid-flash-update don't reference a removed symbol
uint8_t  ch2Sound        = 0;     // 0-7 — selected synth engine, see CH2_SND_NAMES, chosen on the SOUND page
uint8_t  ch2Amount       = 128;   // 0-255, generic live "character" knob via DCY pot (live) — meaning is
                                    // per-engine: FM index, fold drive, ring wet/dry, PWM duty, click length...
#define  CH2_NUM_SOUNDS 16
const char* CH2_SND_NAMES[CH2_NUM_SOUNDS] = {
  "SUBSIN", "DTSQR", "FMBEL", "RINGM", "CLICK", "FOLDR", "PWM", "UNISN",
  "SAW", "SUBDIV", "NOIZ", "VOWEL", "ARPG", "GONG", "CRUSH", "GATE"
};
// CH2_SND_NAMES index reference:
//   0 SUBSIN — sub sine; ch2Amount blends in an octave-up sine (0 = pure
//              sub, max = 50/50 sub+shimmer — the sub stays the foundation)
//   1 DTSQR  — TWO detuned squares (root + ch2DetuneCents via ratio, same
//              scheme as UNISN) summed — real beating/width at any pitch
//   2 FMBEL  — 2-op FM bell/cowbell, ch2Amount = mod index (brightness)
//   3 RINGM  — ring-mod clang (inharmonic carrier x modulator), ch2Amount = wet/dry
//   4 CLICK  — sub sine + short noise-burst attack transient, ch2Amount = burst length/level
//   5 FOLDR  — wavefolded sine, ch2Amount = fold drive
//   6 PWM    — square with ENVELOPE-SWEPT duty: ch2Amount sets the base
//              width, each pulse opens ~25% wider on attack and narrows
//              into the tail — movement per hit, not a static hollow
//   7 UNISN  — two detuned sines summed (thicker sub/pad), uses ch2DetuneCents for spread
//  ── SND2 (pad 2) ──
//   8 SAW    — naive ramp; ch2Amount blends in a second detuned ramp
//              (supersaw-lite width), same trick as DTSQR/UNISN
//   9 SUBDIV — TRUE sub-octave square (divide-by-2 flip-flop) as the
//              FOUNDATION; ch2Amount stacks the root square on top
//              (octaver pedal), 0 = pure sub — never a bare sine
//  10 NOIZ   — xorshift32 noise through a one-pole colour filter;
//              ch2Amount opens it dark->bright and the note's own pitch
//              adds to the cutoff, so it plays from the keyboard
//  11 VOWEL  — fixed-ratio formant stack (root + 2 partials), ch2Amount
//              crossfades "ah"-ish -> "ee"-ish ratios
//  12 ARPG   — internal chiptune arpeggio (root/+7st/+12st cycling on its
//              own phase accumulator), ch2Amount sets the cycle speed
//  13 GONG   — inharmonic FM; ch2Amount sets the RATIO (3.6:1 bell ->
//              7.1:1 sheet metal). The index decays a quarter as fast as
//              the amplitude and never reaches zero, so the metal partial
//              genuinely outlasts the hit at every DCY setting
//  14 CRUSH  — sample-and-hold decimation of the sine (time-domain lo-fi,
//              vs FOLDR's amplitude-domain fold), ch2Amount sets hold length
//  15 GATE   — amplitude chopped by a fast internal (non-harmonic) gate,
//              ch2Amount sets the chop rate — stutter/tremolo texture

// ── CH2 FUNC PAGE ────────────────────────────────────────────────────
// In ch2SynthMode + ch2EditMode, FUNC gets channel 2's OWN 8 slots —
// mirroring how drum mode owns its FUNC set. ch1's FUNC row (KEY/RIFF/
// SOUND/...) is untouched and fully reachable whenever ch2EditMode is
// off; the old FUNC_SOUND hijack (SOUND controlling ch2Sound whenever
// ch2SynthMode was on, leaving ch1's engine unreachable all session)
// is removed — ch2 engine select now lives here as slot 0 (SND1).
// funcSel deliberately stays FUNC_NONE while ch2FuncSel is driving, so
// none of the funcSel==FUNC_PLEN / FUNC_TEMPO special cases at the pad
// call sites can misfire on ch2 slot numbers.
// SND1/SND2 split ch2Sound's 16 engines across two adjacent pads rather
// than a bank-toggle on one — tap either pad, tiles for that half light
// up directly, nothing to flip through first. NOTE (manual note entry)
// is gone — PITCH modes and PATT already cover melodic generation,
// so it had the weakest claim on the freed slot; FOLW (really the whole
// PITCH-mode page, not just literal follow) moved here from slot 1.
const char* CH2FUNCNAMES[8] = {"SND1","SND2","FOLW","ECHO","VERB","PATT","EVOL","REC"};
// DRIFT pot-3 (DCY) label per engine — its "amount" means something
// different on each: order matches ch2Sound 0-15, see CH2_SND_NAMES's
// index reference above. Kept <=4 chars for the bar-label column.
const char* CH2_AMT_LABELS[CH2_NUM_SOUNDS] = {
  "SHMR","DTUN","IDX","MIX","CLK","FOLD","DUTY","DTUN",
  "WDTH","ROOT","TONE","VOWL","SPD","METL","LOFI","CHOP"
};
// PITCH modes. Replaces the old F+8/F-8/F+5/F+3/ARP+/AR+-/WALK set —
// those were either one idea with four fixed knob settings (the F+N
// harmony family) or under-built (ARP+/AR+- had no way to change their
// shape, WALK's random walk never resolved anywhere). FOLW (slot 4) is
// untouched — it's the one mode that was already working well, and its
// slot index has to stay put since ch2PitchMode is a plain 0-7 index
// saved straight to EEPROM (c.pitchMode): reordering it would silently
// reinterpret existing saved patches.
//
// OFF/INV/RNDH (slots 0-2): OFF sits with the FOLLOW group in the label
// list, but isn't a follow variant — it's a static "don't follow ch1"
// mode. INV/RNDH share FOLW's "mirror what ch1 actually sounded"
// mechanism, see the follow branch in triggerCh2Pulse.
//   OFF  = follow disabled — plays ch1's own per-step note directly
//          (scaleNote(seq.cur)), no mirroring/inversion/interval logic
//          on top. Different from FOLW: FOLW tracks the last note ch1
//          actually SOUNDED and holds through ch1's silent steps; OFF
//          reads the CURRENT step's assigned note every time, moving
//          with the pattern regardless of whether ch1 fires on that step.
//   INV  = follow, pitch-inverted around a pivot that ROTATES between
//          root/3rd/5th each trigger (a fixed pivot made INV a pure
//          function of ch1 — repeat ch1's phrase, get an identical
//          mirror every time; rotating the pivot gives INV its own
//          motion even against a static ch1 line)
//   RNDH = follow + a randomly chosen consonant interval per trigger
//          (3rd/5th/6th/octave), instead of one fixed interval forever
//
// CHRD/PDL/ECH1/WALK (slots 3, 5, 6, 7) are key-relative — independent
// of ch1, generate their own motion, and work identically whether or not
// ch1/acid is even running (unlike the FOLLOW family above, which has
// nothing to mirror when ch1 is stopped):
//   CHRD = chord-tone arp cycle (R-3-5-7-9, scale-quality aware)
//   PDL  = pedal-point drone cycle (root-root-5th-octave), not a strict
//          2-note alternation — mostly root, with periodic lift so it
//          doesn't just ping-pong between the same two notes forever
//   ECH1 = fixed "echo" cycle — each chord tone immediately followed by
//          an octave-down repeat of itself (root, root-8ve, 3rd,
//          3rd-8ve, 5th, 5th-8ve), a call-and-answer delay feel from a
//          deterministic shape rather than any runtime note history.
//          Earlier versions followed ch1's or ch2's own trigger history
//          instead — sounded fine while acid was running, but had
//          nothing to echo (and read as silent, or identical to OFF)
//          the moment acid was stopped.
//   WALK = drunk scale-degree walk with gravity back toward the root
const char* CH2_VS_PITCH[8] = {"OFF","INV","RNDH","CHRD","FOLW","PDL","ECH1","WALK"};
// KBRD key labels — chord-tone intervals, see ch2KbIntervalSemis(). Kept
// as its own table (rather than reusing CH2_VS_PITCH) since KBRD has no
// FOLW/CHRD/PDL/WALK slots — it's 8 playable/recordable intervals.
const char* CH2_KB_NAMES[8]  = {"ROOT","3RD","5TH","OCT","2ND","4TH","7TH","-OCT"};
const char* CH2_VS_DCY[8]   = {"25","60","120","250","400","700","1.2S","2S"};
// Per-sample envelope multipliers for {25,60,120,250,400,700,1200,2000}ms
// decay-to--60dB at 16384Hz: envM = 65536*exp(ln(0.001)/(t*16384)).
// Precomputed — the old code ran expf() on every trigger for no reason.
const uint16_t CH2_ENVM[8]  = {64440,65077,65306,65426,65467,65497,65513,65522};
uint8_t ch2FuncSel   = 255;  // 255 = none; 0-7 = CH2FUNCNAMES index
uint8_t ch2PitchMode = 0;    // 0-7, see CH2_VS_PITCH
uint8_t ch2DecaySel  = 4;    // default 400ms — matches the old fixed feel
uint8_t ch2ArpPos    = 0;    // CHRD/PDL cycle position, advances per trigger
// Base phase the arp cycle restarts from at the top of each pattern cycle.
// Repeatability: ch2ArpPos free-ran, so unless the hit count per bar
// happened to be a multiple of the cycle length the tone landing on a
// given step drifted every bar and never lined up twice. Also the hook a
// future pattern-rotation feature would use to rotate CHRD/PDL's TONE
// ASSIGNMENT in sync with a rotated ch1 pattern — nothing in this file
// currently writes anything other than 0 here, so that's aspirational
// for now, not live behavior.
uint8_t ch2ArpPhase  = 0;
int8_t  ch2WalkDeg   = 0;    // WALK: current scale-degree offset (also
                              // doubles as "distance from root" for the
                              // v2 gravity bias, see ch2IntervalSemis)

// ── CH2 ECHO ─────────────────────────────────────────────────────────
// Tempo-synced delay on the ch2 voice only, rendered on core 1 inside
// bmFillDrumBufferTo() (see the echo block there). Division presets, not
// milliseconds — free-time echo fights a step sequencer's groove.
// 16KB buffer = 500ms ceiling: a 1/4-note delay is exact down to 120 BPM
// and clamps to ~500ms below that (still musical, just no longer a true
// quarter). Power-of-two length so core 1 wraps with a mask, not a div.
// If the linker ever reports RAM overflow, this buffer is the first
// thing to shrink — drop to 4096/int16 and accept the 250ms ceiling.
#define CH2_ECHO_LEN 16384           // samples; MUST stay a power of two.
                                     // Doubled from 8192 when the preset set
                                     // gained 4D and 1/2 divisions: a half-
                                     // note at 120 BPM is a full second, and
                                     // a tile that silently clamps to half
                                     // its labeled time is a lie. 32KB —
                                     // the largest RAM object in the build;
                                     // still the first thing to shrink if
                                     // the linker reports overflow.
int16_t  ch2EchoBuf[CH2_ECHO_LEN];   // 16KB BSS — zeroed at boot
volatile uint16_t ch2EchoDelay = 0;  // samples, 0 = echo off; core0 writes, core1 reads
volatile uint8_t  ch2EchoFb    = 0;  // feedback, Q8 (x/256)
uint8_t  ch2EchoSel = 0;             // 0-7, see CH2_VS_ECHO
// 16TH and 8TH removed after hardware testing: at typical tempos those
// delays (125/250ms) land UNDER the pulse's own decay tail (default
// 400ms) — the repeat is masked by the still-ringing source. Not a bug,
// physics: echoes shorter than the source's decay hide inside it.
// Replaced with LONGER divisions (4D, 1/2) that ring into clear air.
// 8FB kept: an 8th WITH feedback repeats past the tail, so it was
// always audible.
const char* CH2_VS_ECHO[8] = {"OFF","8D","1/4","4D","1/2","8FB","4FB","2FB"};

// ── CH2 VERB ─────────────────────────────────────────────────────────
// Lo-fi Schroeder reverb on the ch2 voice only, rendered on core 1 after
// the echo (repeats get reverberated) and before bmSoftClip. 4 parallel
// feedback combs with one-pole damping in each loop → 2 series allpasses.
// Comb lengths are PRIMES scaled from Schroeder's classic 30-41ms to
// 16384Hz — mutually prime so the resonant modes interleave instead of
// stacking into one metallic pitch. At this rate/width it is knowingly
// grainy and dark — dusty-spring territory, not a hall; that's the
// instrument's aesthetic, accepted up front.
#define CH2_VERB_C0 487
#define CH2_VERB_C1 541
#define CH2_VERB_C2 641
#define CH2_VERB_C3 677
#define CH2_VERB_A0 83
#define CH2_VERB_A1 29
#define CH2_VERB_DAMP 112   // Q8 one-pole damping in each comb loop (~0.44)
struct Ch2VerbBufs {        // one struct so BeatMachine2 externs ONE symbol
  int16_t c0[CH2_VERB_C0], c1[CH2_VERB_C1], c2[CH2_VERB_C2], c3[CH2_VERB_C3];
  int16_t a0[CH2_VERB_A0], a1[CH2_VERB_A1];
};
Ch2VerbBufs ch2VerbBufs;                  // ~4.9KB BSS — zeroed at boot
volatile uint8_t ch2VerbFbQ8  = 0;        // comb feedback (room size), Q8
volatile uint8_t ch2VerbWetQ8 = 0;        // wet mix, Q8; 0 = verb off entirely
uint8_t ch2VerbSel = 0;                   // 0-7, see CH2_VS_VERB
const char* CH2_VS_VERB[8] = {"OFF","SML","MED","BIG","HALL","MEDW","BIGW","WASH"};

// ── CH2 EUC / HARM / STUT — sequencer-side, no DSP ───────────────────
// EUC: per-slot user pattern loader, WRITTEN INTO ch2Steps — destructive
// on purpose, it's a groove preset loader. All 8 slots start blank; hold a
// tile to save the current ch2Steps into it, tap to load it back (see
// ch2LoadEucSlot/Ch2EucSlots above). ch2EucSel is display-only (highlights
// the last slot loaded/saved this session); the PATTERN is what persists,
// via ch2EucCustom[]/Ch2EucSlots in EEPROM.
uint8_t ch2EucSel  = 255;  // 255 = no highlight
const char* CH2_VS_EUC[8]  = {"S1","S2","S3","S4","S5","S6","S7","S8"};
// EUC hold-to-save gesture, one tile at a time — heldMs/ch2GestPad/
// ch2GestArmed (declared just below) are shared across every ch2 FUNC page.
#define CH2_EUC_SAVE_HOLD_MS 600
#define CH2_EUC_FLASH_MS     300
int8_t   ch2EucFlashTile = -1;     // tile to pulse white after a save, -1 = none
uint32_t ch2EucFlashMs   = 0;
// ── CH2 LIVE PLAYABILITY ─────────────────────────────────────────────
// A HELD key on the KBRD page transposes the running DRIFT line — you
// perform, live, without touching the recorded pattern. ch2GestSince/
// ch2GestPad/ch2GestArmed time every top-row hold and are shared across
// every ch2 FUNC page (KBRD transpose, EUC/PATT's hold-to-save, formerly
// HARM's bar-count programming) — one hold-timer, many pages reading it.
int16_t  ch2XposeSemis   = 0;    // live transpose applied to DRIFT playback
int8_t   ch2XposeKey     = -1;   // top-row pad driving it, -1 = none
uint32_t ch2GestSince    = 0;    // when the currently-held top-row pad went down
int8_t   ch2GestPad      = -1;   // which top-row pad is being timed
bool     ch2GestArmed    = false;// this hold already fired its one-shot action
// EVOLVE v2: replaces the v1 shadow-array mutator entirely (swap/nudge/
// duplicate/remove — see git history). v1 mutated a persistent shadow copy
// of the pattern one small step at a time, independently per mutation
// event; it never converged on anything predictable, and there was no way
// to get "this specific thing happens, then reverts, then a different
// specific thing happens" out of it — every mode was the same generic
// algorithm at a different dial setting.
//
// v2 is a ROOT/EXCURSION cadence instead: the pattern plays exactly as
// recorded for a fixed number of bars (root), then a mode-specific effect
// applies for a fixed number of bars (excursion), then back to root, on
// repeat. Each of the 7 presets is now a genuinely distinct, named effect
// (octave shifts, an extra step, a stutter, or combinations), not one
// algorithm scaled by intensity.
//
// Implemented as a LIVE OVERLAY, same principle as the old HARM offset and
// ch2XposeSemis: nothing in ch2Steps/ch2StepNote is ever touched. This
// replaces v1's shadow-copy approach (ch2EvoSteps/ch2EvoStepNote/
// ch2EvoAdded, all gone) with something structurally simpler — an
// excursion's parameters are computed fresh when it STARTS and just stop
// being read when it ENDS, so there's no persistent divergent state to
// resync or accidentally leave stale. That simplicity is deliberate: v1
// shipped two real bugs from having too much state to keep synchronized.
uint8_t ch2EvolSel = 0;    // 0 = OFF, 1-7 = mode preset, see CH2_VS_EVOL
const char* CH2_VS_EVOL[8] = {"OFF","OCTL","ADD1","DEEP","STUT","HVY","WILD","MAX"};

// What an excursion actually DOES. Two independent dimensions, either or
// both active per mode:
//  - Octave overlay (ch2EvoOctOffset, semitones) — added to every pitch
//    path in triggerCh2Pulse, same guard ch2XposeSemis uses (skipped for a
//    live NOTE-key press — you pressed that note, EVOLVE doesn't get to
//    override your hands).
//  - Extra step (ch2EvoExtraStep/ch2EvoExtraNote) — one specific step,
//    chosen fresh each excursion, force-triggers for the excursion's
//    duration with a chosen note, whether or not that step was originally
//    on. STUT reuses the exact same mechanism but always targets the step
//    immediately after an already-active one, so it reads as a ratchet
//    rather than a fill appearing from nowhere.
#define CH2_EVO_KIND_OCT_ALT   1   // octave shift, alternates/varies each excursion
#define CH2_EVO_KIND_ADD_STEP  2   // one extra step appears, reverts after
#define CH2_EVO_KIND_OCT_DEEP  3   // octave shift, always DOWN, amount varies
#define CH2_EVO_KIND_STUTTER   4   // duplicate an active step onto the next one
#define CH2_EVO_KIND_ADD_OCT   5   // extra step AND octave shift together (HVY/MAX)
#define CH2_EVO_KIND_RANDOM    6   // WILD — fresh random pick each excursion among
                                    // oct-up / oct-down / extra-step
struct Ch2EvoPreset { uint8_t rootBars; uint8_t excBars; uint8_t kind; };
const Ch2EvoPreset CH2_EVO_PRESET[8] = {
  {1, 1, 0},                              // 0 OFF — unused, guarded out before lookup
  {3, 1, CH2_EVO_KIND_OCT_ALT},            // 1 OCTL — 3 bars root, 1 bar octave lift, repeat
  {3, 1, CH2_EVO_KIND_ADD_STEP},           // 2 ADD1 — one extra step, mostly root
  {3, 1, CH2_EVO_KIND_OCT_DEEP},           // 3 DEEP — occasional low octave dip
  {2, 1, CH2_EVO_KIND_STUTTER},            // 4 STUT — a ratchet every 3rd bar
  {2, 1, CH2_EVO_KIND_ADD_OCT},            // 5 HVY  — extra step + octave, every 3rd bar
  {1, 1, CH2_EVO_KIND_RANDOM},             // 6 WILD — random pick, every other bar
  {1, 1, CH2_EVO_KIND_ADD_OCT},            // 7 MAX  — extra step + octave, every other bar
};

bool     ch2EvoInExcursion = false;   // which segment of the cadence we're in
uint16_t ch2EvoStepsInSeg  = 0;       // steps elapsed in the current segment,
                                       // vs (rootBars or excBars)*16 — same
                                       // unconditional-count-then-act-at-lap-
                                       // end shape HARM's auto-walk used.
int8_t   ch2EvoOctOffset   = 0;       // live semitone offset, 0 = root/no effect
int8_t   ch2EvoExtraStep   = -1;      // step index force-triggered this excursion, -1 = none
int8_t   ch2EvoExtraNote   = CH2_STEP_NONE;  // the note that forced step plays
int8_t   ch2EvoLastOctDir  = 0;       // previous excursion's octave choice, so
                                       // "a slightly different note next time"
                                       // doesn't just repeat the same one twice
int8_t   ch2EvoLastExtraStep = -1;    // previous excursion's extra-step choice,
                                       // same reasoning — vary it, don't repeat

// Which source triggerCh2Pulse/the trigger gate should read. No shadow copy
// in v2 — ch2Steps/ch2StepNote are read directly; the only overlay is one
// possible FORCED extra step during an excursion, computed fresh each time
// (see ch2EvoStartExcursion below), never stored.
inline bool ch2EvoStepOn(uint8_t i) {
  if (ch2Steps[i]) return true;
  return ch2EvolSel && ch2EvoInExcursion && ch2EvoExtraStep == (int8_t)i;
}
inline int8_t ch2EvoNoteAt(uint8_t i) {
  if (ch2Steps[i]) return ch2StepNote[i];   // recorded note always wins
  if (ch2EvolSel && ch2EvoInExcursion && ch2EvoExtraStep == (int8_t)i) return ch2EvoExtraNote;
  return CH2_STEP_NONE;
}

// Called once, the instant an excursion BEGINS (root -> excursion). Picks
// this excursion's octave offset and/or extra step based on the mode's
// kind, biased away from repeating whatever the previous excursion did —
// "changes again to a slightly different note" rather than the same
// change every time. Nothing here persists past the excursion; there's
// nothing to undo when it ends, only overlay reads to stop happening.
void ch2EvoStartExcursion() {
  ch2EvoOctOffset = 0; ch2EvoExtraStep = -1; ch2EvoExtraNote = CH2_STEP_NONE;
  uint8_t kind = CH2_EVO_PRESET[ch2EvolSel].kind;

  bool wantOct = (kind == CH2_EVO_KIND_OCT_ALT || kind == CH2_EVO_KIND_OCT_DEEP ||
                  kind == CH2_EVO_KIND_ADD_OCT);
  bool wantAdd = (kind == CH2_EVO_KIND_ADD_STEP || kind == CH2_EVO_KIND_ADD_OCT);
  bool wantStut = (kind == CH2_EVO_KIND_STUTTER);

  if (kind == CH2_EVO_KIND_RANDOM) {   // WILD — fresh 3-way pick every time
    uint8_t r = (uint8_t)random(3);
    wantOct = (r != 2); wantAdd = (r == 2);
  }

  if (wantOct) {
    int8_t dir;
    if (kind == CH2_EVO_KIND_OCT_DEEP) {
      // always down, but vary the AMOUNT (1 or 2 octaves) so it's not the
      // exact same dip every time
      dir = (ch2EvoLastOctDir == -1) ? -2 : -1;
    } else {
      // alternate up/down, one octave each way — avoid repeating last time
      dir = (ch2EvoLastOctDir >= 0) ? -1 : 1;
      if (kind == CH2_EVO_KIND_RANDOM) dir = random(2) ? 1 : -1;  // WILD: no memory bias
    }
    ch2EvoOctOffset  = (int8_t)(dir * 12);
    ch2EvoLastOctDir = dir;
  }

  if (wantAdd) {
    uint8_t cand[NUM_STEPS], n = 0;
    for (uint8_t i = 0; i < NUM_STEPS; i++)
      if (!ch2Steps[i] && (int8_t)i != ch2EvoLastExtraStep) cand[n++] = i;
    if (n == 0)   // everything's on, or the only free slot was last time's — allow a repeat
      for (uint8_t i = 0; i < NUM_STEPS; i++) if (!ch2Steps[i]) cand[n++] = i;
    if (n > 0) {
      uint8_t pick = cand[random(n)];
      ch2EvoExtraStep    = (int8_t)pick;
      ch2EvoLastExtraStep = (int8_t)pick;
      // borrow the note from the nearest active step so the extra hit is
      // harmonically related to what's actually playing, not an arbitrary
      // interval — falls back to ROOT if the pattern has no active steps at all
      int8_t note = CH2_STEP_NONE;
      for (uint8_t d = 1; d < NUM_STEPS && note == CH2_STEP_NONE; d++) {
        uint8_t a = (pick + d) % NUM_STEPS, b = (pick + NUM_STEPS - d) % NUM_STEPS;
        if (ch2Steps[a] && ch2StepNote[a] != CH2_STEP_NONE) note = ch2StepNote[a];
        else if (ch2Steps[b] && ch2StepNote[b] != CH2_STEP_NONE) note = ch2StepNote[b];
      }
      ch2EvoExtraNote = (note == CH2_STEP_NONE) ? 0 : note;   // 0 = ROOT
    }
  }

  if (wantStut) {
    uint8_t cand[NUM_STEPS], n = 0;
    for (uint8_t i = 0; i < NUM_STEPS; i++) {
      uint8_t nxt = (i + 1) % NUM_STEPS;
      if (ch2Steps[i] && ch2StepNote[i] != CH2_STEP_NONE && !ch2Steps[nxt]) cand[n++] = i;
    }
    if (n > 0) {
      uint8_t src = cand[random(n)];
      ch2EvoExtraStep = (int8_t)((src + 1) % NUM_STEPS);
      ch2EvoExtraNote = ch2StepNote[src];
    }
  }
  ui.dirty = true;   // no per-cell marker currently renders EVOLVE's excursion
                      // state (ch2EvoExtraStep/ch2EvoInExcursion are read-only
                      // audio-timing flags — see ch2EvoStepOn/ch2EvoNoteAt, not
                      // drawn anywhere in drawStepCellEx), so there's nothing
                      // on screen that actually needs repainting here. This
                      // used to also set cellsDirty/cellIdx=0, which swept a
                      // full 16-cell redraw across whichever screen was up —
                      // acid's grid or DRIFT's — every time EVOLVE flipped
                      // segments (periodic, tied to the pattern loop). That's
                      // the visible "steps redrawing after every loop" you'd
                      // see with EVOLVE on, for no actual visual change.
}

// Called once, the instant an excursion ENDS (excursion -> root). Nothing
// to restore — the overlay reads (ch2EvoStepOn/ch2EvoNoteAt/the octave add
// in triggerCh2Pulse) all already gate on ch2EvoInExcursion, so clearing
// the flag is the entire revert. This is the payoff of not having a
// shadow copy: reverting can't desync because there's nothing to desync.
void ch2EvoEndExcursion() {
  ch2EvoOctOffset = 0; ch2EvoExtraStep = -1; ch2EvoExtraNote = CH2_STEP_NONE;
  ui.dirty = true;   // see ch2EvoStartExcursion() above — same reasoning,
                      // no cellsDirty sweep needed, nothing visual to revert.
}
// Force back to the ROOT segment and zero the cadence counter. Called
// everywhere the real pattern changes under EVOLVE's feet (record, clear,
// PATT load, patch load, manual grid edit) or EVOLVE turns on from OFF —
// same call sites v1's ch2EvoResync() used, same reasoning (don't let
// state computed against the OLD pattern keep being read against a new
// one), just a much smaller thing to reset now that there's no shadow copy.
void ch2EvoResetCadence() {
  if (ch2EvoInExcursion) ch2EvoEndExcursion();
  ch2EvoInExcursion = false;
  ch2EvoStepsInSeg  = 0;
}


// Hold threshold. Must clear a normal record-tap on the KBRD page
// (~50-100ms) so a quick note entry doesn't blip the line.
#define CH2_XPOSE_HOLD_MS   180
// NOTE page press-flash. Declared up here rather than beside ch2NotePlay()
// because ch2PollLiveGestures() (below, but earlier in the file) now sets
// them too — a global has to be declared before its first use in the TU.
uint32_t gCh2NotePressMs  = 0;   // millis() of the last NOTE key press
uint8_t  gCh2NotePressIdx = 0;   // which key, for the press-flash above

// ── CH2 REC (pot-motion recorder) — TOGGLE model. Short-tap the REC pad
// (16) to start/stop recording; long-press to clear. While recording,
// any pot you move arms its lane and its motion is captured per step.
bool ch2Recording = false;

// ── POT-MOTION RECORDER ──────────────────────────────────────────────
// Three lanes matching the DRIFT pots: 0=OCT(cut), 1=AMT(res), 2=DCY.
// Hold pad 16 (REC) and move a pot: that lane arms on movement and its
// value is written to the current playhead step each control tick, so one
// loop of the pattern captures the motion. Release REC and recorded lanes
// play back per step (advanceStep) while un-recorded pots stay live. Re-tap
// the REC pad to clear all lanes. Stored as raw pot >> 2 (0-255/step).
uint8_t  ch2AutoVal[3][NUM_STEPS] = {{0}};  // recorded value per lane per step
uint8_t  ch2AutoRec   = 0;           // bit L set = lane L has a recording
uint8_t  ch2RecActive = 0;           // bit L set = actively recording now (transient)
int      ch2RecSnap[3] = {-1,-1,-1}; // raw pot at REC-arm, for move detection
bool     ch2PrevRecArmed = false;
uint32_t gCh2RecClrFlashMs = 0;      // clear-all ack flash timer

// Apply a raw pot value (0-1023) to a DRIFT lane's parameter. Shared by
// live reads, recording, and playback so all three map identically.
void ch2ApplyPotRaw(uint8_t lane, int raw) {
  raw = constrain(raw, 0, 1023);
  switch (lane) {
    case 0: ch2Octave = (int8_t)((raw * 5L) / 1024) - 2; ch2OctDisplay = (uint16_t)raw; break;
    case 1:
      if (ch2Sound == 1 || ch2Sound == 7) ch2DetuneCents = (int16_t)((raw * 30L) / 1023);
      else                                ch2Amount      = (uint8_t)(raw >> 2);
      ch2AmtDisplay = (uint16_t)raw;
      break;
    case 2: {                                                     // log decay 25ms..2s
      float t = 0.025f * powf(80.0f, (float)raw / 1023.0f);
      ch2EnvMLive   = (uint16_t)(65536.0f * expf(logf(0.001f) / (t * (float)AUDIO_RATE)));
      ch2DcyDisplay = (uint16_t)raw;
    } break;
  }
}

// Per-step automation playback: for each recorded lane not being actively
// recorded, apply its stored value for the current step. Runs whenever
// DRIFT plays (edit mode or under the acid screen).
void ch2AutoPlayback() {
  if (!ch2AutoRec) return;
  for (uint8_t L = 0; L < 3; L++)
    if ((ch2AutoRec & (1 << L)) && !(ch2RecActive & (1 << L)))
      ch2ApplyPotRaw(L, (int)ch2AutoVal[L][seq.cur] << 2);
}

// Last note ch1 actually SOUNDED (0-59 noteFreq index), captured inside
// triggerNote() so it includes ratchets, stutters, and effect-transposed
// pitches (Oct Up, chord-step arps). -1 until the first audible note.
// The FOLLOW-family pitch modes (INV/RNDH/FOLW) read this instead of
// the current step's STORED note, so ch2 tracks what you actually hear —
// a silent ch1 step no longer yanks ch2 to a pitch that was never played.
// Last note index ch1 ACTUALLY fired (captured in triggerNote(), the one
// choke point every ch1 voice pass goes through — steps, riffs, walks).
// -1 until the first note of the session; the FOLLOW family falls back
// to the current step's stored note only in that window. int16_t on
// purpose: a uint8_t with a 255 sentinel would make the >=0 check
// always-true and pin the follow to a garbage top note before ch1 ever
// plays.
int16_t gLastCh1Note = -1;

// Publish verb params for the current preset. No tempo dependency, so
// unlike echo this only needs calling from apply + load — not per trigger.
void ch2ApplyVerb() {
  // WET retuned upward alongside the structural sum>>2 -> sum>>1 fix in
  // the DSP (see BeatMachine2): the original scaling left the wet path
  // ~30dB below dry — inaudible under a playing pattern. Now lands
  // roughly -15dB (SML) to -6dB (WASH): present without swamping.
  //                     OFF SML MED BIG HALL MEDW BIGW WASH
  static const uint8_t FB[8]  = {0,154,184,205,220, 184, 205, 225};
  static const uint8_t WET[8] = {0, 96,120,140,140, 190, 190, 240};
  uint8_t s = ch2VerbSel & 7;
  ch2VerbFbQ8  = FB[s];
  ch2VerbWetQ8 = WET[s];
}
volatile uint32_t ch2Phase    = 0;      // oscillator phase accumulator
volatile uint32_t ch2PhaseInc = 0;      // phase increment per sample, set on trigger
volatile uint16_t ch2Env      = 0;      // 8.8 fixed-point envelope level — 0 = silent
volatile uint16_t ch2EnvM     = 65490;  // per-sample decay multiplier (~400ms to near-silent at 16384Hz)
volatile uint32_t ch2DetuneRatioQ16 = 65536;  // Q16 second-voice ratio (1 + cents/1731), set every
                                              // trigger — shared by BOTH dual-osc engines (DTSQR, UNISN)
volatile uint8_t  ch2ClickCount = 0;     // CLICK: samples of noise-burst attack remaining
volatile uint8_t  ch2NoiseIdx   = 0;     // CLICK + NOIZ: running index into noisetable[] for the burst
#define  CH2_CLICK_LEN_MAX 24            // CLICK: longest burst at ch2Amount==255, ~1.5ms @16384Hz
// ── SND2 (engines 8-15) new persistent state — see Drift.ino's engine
// switch for how each is used, and triggerCh2Pulse() for where they're
// reset. Same cost class as ch2ClickCount/ch2NoiseIdx above.
volatile uint8_t  ch2SubDivFlip = 0;     // SUBDIV: divide-by-2 flip-flop
volatile int16_t  ch2CrushHold  = 0;     // CRUSH: currently-held sample value
volatile uint8_t  ch2CrushCtr   = 0;     // CRUSH: samples remaining before the next hold
volatile uint32_t ch2ArpgPhase  = 0;     // ARPG: its own phase accumulator
volatile uint8_t  ch2ArpgStep   = 0;     // ARPG: which of the 3 ratios is current (0-2)
volatile uint16_t ch2ArpgCtr    = 0;     // ARPG: samples remaining at the current step (needs >255)
volatile uint16_t ch2GongIdx    = 0;     // GONG: independent FM-index decay
volatile uint32_t ch2NoiseLfsr  = 0x1234567;  // NOIZ: xorshift32 noise state (never 0)
volatile int16_t  ch2NoiseLp    = 0;     // NOIZ: one-pole lowpass state (colour filter)
volatile uint32_t ch2NoisePhase = 0;     // NOIZ: clock accumulator — sets noise pitch from the note
volatile uint32_t ch2VowP1      = 0;     // VOWEL: formant-1 phase (absolute Hz, not a ratio)
volatile uint32_t ch2VowP2      = 0;     // VOWEL: formant-2 phase
volatile uint32_t ch2GatePhase  = 0;     // GATE: chop phase, free-running and pitch-independent
uint32_t syncMs=0;
#define  SYNCTOUT 2000

// Legacy sync state from the old PPQN tempo-derivation model — no longer used
// by the direct-clock engine (see SYNC_STEPS_PER_PULSE). syncPulse is retained
// only because a few reset sites still write it (harmless); nothing reads it.
uint8_t  syncPulse   = 0;

// =====================================================================
// HELPERS
// =====================================================================
uint32_t    bpm2us(uint16_t b)  { return 60000000UL / b / 4; }
const char* nName(uint8_t i)    { return NNAMES[i % 12]; }
uint8_t     nOct(uint8_t i)     { return i / 12; }

// =====================================================================
// FUNCTION BUTTON MAPS
// =====================================================================
const uint8_t KEY_MAP[8]    = {0,2,3,5,7,8,10,11};  // C D Eb F G Ab Bb B
const uint8_t SOUND_MAP[8]  = {0,1,2,8,4,5,6,9};    // pad4=PWM(8), pad8=Sub Square(9)
const uint8_t PLEN_MAP[8]   = {1,2,3,4,6,8,12,16};
const uint8_t FX_CYCLE[]    = {0,1,2,3,4,5,6,7};
#define FX_CYCLE_LEN (sizeof(FX_CYCLE)/sizeof(FX_CYCLE[0]))
const uint8_t FX_PAD_MAP[8] = {0,1,2,3,4,5,6,7};    // None OctUp Retrig Stutter MajStep MinStep Dom7Step DimStep

// =====================================================================
// NOTE TRIGGER
// =====================================================================
void triggerNote(uint8_t freqIdx, bool accent, bool gl) {
  gLastCh1Note = freqIdx;  // FOLW source — see declaration
  uint16_t f = noteFreq[constrain((int)freqIdx, 0, 59)] / 2;

  if ((gl || gPorta) && seq.running && f != gFreq) {
    int32_t ticks;
    if (gl) {
      ticks = (int32_t)((uint64_t)seq.interval * MOZZI_CONTROL_RATE / 1000000UL);
      if (ticks < 2) ticks = 2;
    } else {
      // portamento: speed 1-8 → ticks 32,24,16,12,8,6,4,2
      const uint8_t portaTicks[8] = {32,24,16,12,8,6,4,2};
      ticks = portaTicks[gPortaSpeed - 1];
    }
    gTarget    = f;
    int32_t diff = ((int32_t)f - (int32_t)gFreq) << 8;
    gGlideStep = diff / ticks;
    if (gGlideStep == 0) gGlideStep = (diff > 0) ? 1 : -1;
    gGlide     = true;
  } else {
    gFreq   = f;
    gFreqFP = (int32_t)f << 8;
    gGlide  = false;
    cnt     = 0;
  }

  gVolSub    = accent ? -60 : 30;  // accent = boosted above full volume, normal = slight attenuation
  gEnvCutoff = accent ? (int16_t)min((int)gEnvCutNorm * 2, 255) : gEnvCutNorm;  // 303 cutoff sweep (needs CUT pot low); accent auto-scales
  gEnvRes    = accent ? ACCENT_RES_FIXED    : ENV_RES_NORMAL;     // resonance sweep (caps at gResCap)
  gAccentActive = accent;  // accented notes get a slower filter-envelope decay (303-style "wah")
  gLastStepMs= millis();
}

// CHANNEL 2 — a rhythmic pulse layer, not a melodic voice. Fires from
// advanceStep() whenever ch2Steps[seq.cur] is on, independent of whatever
// channel 1 is doing on that same step (channel 2 has no notes of its own
// to trigger — see triggerCh2Pulse() below). Pitch always tracks channel
// 1's current root key, so changing key never leaves channel 2 clashing.
// Publish echo params for the current preset + CURRENT tempo. Called from
// ch2FuncApply (immediate response to a tile press) and from every
// triggerCh2Pulse (so tempo changes — FUNC TEMPO, tap tempo — retune the
// delay time without any extra plumbing at the tempo call sites; between
// triggers the tail simply rings at the old time, which is fine).
// One integer divide per trigger; core 1 reads the two volatiles.
void ch2ApplyEcho() {
  // preset:            OFF  8D 1/4  4D 1/2  8FB 4FB 2FB
  static const uint8_t M[8]  = {0,  3,  4,  6,  8,  2,  4,  8};  // x 16th
  static const uint8_t FB[8] = {0, 76, 76, 76, 76,168,168,168};  // Q8
  uint8_t s = ch2EchoSel & 7;
  if (M[s] == 0) { ch2EchoDelay = 0; ch2EchoFb = 0; return; }
  // samples per 16th at AUDIO_RATE 16384: (60/tempo/4)*16384 = 245760/tempo
  uint32_t d = ((uint32_t)M[s] * 245760UL) / (uint32_t)seq.tempo;
  ch2EchoDelay = (uint16_t)constrain(d, (uint32_t)1, (uint32_t)(CH2_ECHO_LEN - 1));
  ch2EchoFb    = FB[s];
}
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
