lonesoulsurfer/Acid_Drip_Bassline_and_Drum_Synth/src/Acid_Drip_Drum_Acid_Drift_V5/beats.h

// Beat patterns for Beat Machine 2 — tuned for acid/techno/house
// Drum order: kick, hat, snare, rim, tom, bass2, clap, openhat
// Each row = 4 bytes = 32 steps (2 bars of 16th notes)
// Bit 7 of byte 0 = step 1, bit 6 = step 2 ... bit 0 of byte 3 = step 32

#define NUM_BEATS 16

const byte beats[NUM_BEATS][8][4] PROGMEM = {

  { // 1. BASIC — simple 4/4, clean foundation for any acid line
    {0b10001000,0b10001000,0b10001000,0b10001000,},  // kick: 1 3 5 7 (every beat)
    {0b00100010,0b00100010,0b00100010,0b00100010,},  // hat: offbeats (2 4 6 8)
    {0b00001000,0b00001000,0b00001000,0b00001000,},  // snare: 3 7 (2 and 4)
    {0b00000000,0b00000000,0b00000000,0b00000000,},
    {0b00000000,0b00000000,0b00000000,0b00000000,},
    {0b00000000,0b00000000,0b00000000,0b00000000,},  // bass2: unused
    {0b00000000,0b00000000,0b00000000,0b00000000,},  // clap: unused
    {0b00000000,0b00000000,0b00000000,0b00000000,},  // openhat: unused
  },

  { // 2. HOUSE — four-on-floor kick, open hat offbeat, snare 2+4
    {0b10001000,0b10001000,0b10001000,0b10001000,},  // kick: every beat
    {0b10101010,0b10101010,0b10101010,0b10101010,},  // hat: every 8th
    {0b00001000,0b00001000,0b00001000,0b00001000,},  // snare: 2+4
    {0b00000000,0b00000000,0b00000000,0b00000000,},
    {0b00000000,0b00000000,0b00000000,0b00000000,},
    {0b00000000,0b00000000,0b00000000,0b00000000,},  // bass2: unused
    {0b00000000,0b00000000,0b00000000,0b00000000,},  // clap: unused
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
    {0b10001010,0b00101000,0b10001010,0b00101000,},  // tom: driving rhythm
    {0b00000000,0b00000000,0b00000000,0b00000000,},  // bass2: unused
    {0b00000000,0b00000000,0b00000000,0b00000000,},  // clap: unused
    {0b00000000,0b00000000,0b00000000,0b00000000,},  // openhat: unused
  },

  { // 16. JACK — classic jackin' house groove: four-on-the-floor kick, the
    // signature "jack" clap pattern (hits 2,5,9,13 in bar1, 3,5,9,11 in
    // bar2) driving the groove forward, kick-reinforcing snare on beats
    // 1-3 of each bar, sparse ghost rim 16ths, and offbeat open hats
    {0b10001000,0b10001000,0b10001000,0b10001000,},  // kick: four-on-the-floor
    {0b11111111,0b11111111,0b11111111,0b11111111,},  // hat: driving 16ths
    {0b10001000,0b10000000,0b10001000,0b10000000,},  // snare: reinforces kick on beats 1-3
    {0b00000100,0b00000100,0b00000100,0b00000100,},  // rim: sparse ghost 16ths
    {0b00000000,0b00000000,0b00000000,0b00000000,},
    {0b00000000,0b00000000,0b00000000,0b00000000,},  // bass2: unused
    {0b01001000,0b10001000,0b00101000,0b10100000,},  // clap: "the jack" — 2,5,9,13/3,5,9,11
    {0b00100010,0b00100010,0b00100010,0b00100010,},  // openhat: offbeat lift
  },

};
