lonesoulsurfer/Acid_Drip_Bassline_and_Drum_Synth/src/Acid_Drip_Drum_Acid_Drift_V5/sample0.h

#ifndef sample0_H_
#define sample0_H_
 
#if ARDUINO >= 100
#include "Arduino.h"
#else
#include "WProgram.h"
#endif
#include "mozzi_pgmspace.h"
 
#define sample0_NUM_CELLS 6013
#define sample0_SAMPLERATE 16384
 
CONSTTABLE_STORAGE(int8_t) sample0_DATA [] = {
0, 1, 9, 24, 43, 53, 60, 68, 73, 80, 84, 88, 91, 93, 96, 99, 
99, 99, 96, 92, 86, 81, 75, 70, 64, 57, 50, 43, 36, 29, 22, 15, 
7, -2, -9, -15, -22, -29, -36, -44, -50, -57, -63, -69, -75, -81, -86, -92, 
-97, -102, -105, -109, -113, -116, -120, -122, -124, -124, -125, -125, -125, -124, -123, -123, 
-122, -120, -120, -119, -117, -115, -113, -111, -108, -105, -102, -99, -95, -91, -86, -81, 
-78, -71, -67, -62, -57, -51, -45, -39, -33, -26, -20, -15, -9, -4, 2, 5, 
11, 13, 17, 21, 24, 27, 29, 31, 34, 36, 38, 40, 43, 45, 46, 47, 
49, 50, 52, 54, 56, 56, 57, 59, 59, 61, 62, 63, 64, 65, 66, 66, 
67, 67, 68, 69, 69, 70, 70, 70, 70, 72, 72, 72, 72, 72, 73, 73, 
73, 73, 73, 73, 72, 72, 73, 73, 71, 71, 72, 71, 70, 70, 70, 69, 
69, 68, 68, 67, 66, 65, 66, 65, 63, 63, 63, 61, 60, 59, 59, 58, 
57, 56, 56, 54, 53, 52, 51, 49, 49, 48, 46, 45, 43, 44, 42, 41, 
39, 39, 37, 36, 34, 33, 32, 30, 29, 29, 28, 26, 25, 23, 22, 19, 
18, 17, 16, 14, 13, 12, 9, 8, 6, 4, 3, 1, -1, -2, -3, -6, 
-7, -9, -11, -13, -15, -16, -18, -19, -22, -24, -27, -28, -30, -32, -35, -37, 
-40, -41, -44, -45, -48, -51, -53, -55, -57, -59, -62, -63, -65, -67, -70, -72, 
-75, -76, -78, -81, -82, -84, -86, -88, -90, -92, -94, -96, -98, -98, -101, -102, 
-103, -104, -106, -107, -108, -109, -110, -112, -113, -114, -115, -116, -115, -116, -117, -117, 
-118, -118, -119, -119, -119, -119, -119, -118, -118, -118, -118, -117, -116, -115, -115, -114, 
-114, -111, -111, -109, -107, -104, -103, -102, -100, -98, -97, -94, -92, -90, -87, -86, 
-83, -80, -78, -75, -72, -70, -68, -64, -62, -59, -57, -55, -52, -49, -46, -44, 
-41, -38, -35, -33, -29, -28, -23, -22, -18, -17, -14, -12, -9, -6, -5, -2, 
1, 3, 7, 8, 12, 14, 17, 19, 21, 24, 27, 28, 29, 31, 34, 37, 
38, 40, 43, 45, 47, 49, 51, 53, 54, 57, 59, 61, 62, 64, 66, 67, 
69, 70, 72, 73, 74, 75, 77, 78, 80, 81, 83, 84, 85, 87, 88, 88, 
90, 92, 92, 94, 94, 96, 96, 97, 97, 98, 99, 100, 100, 100, 102, 102, 
103, 103, 103, 103, 104, 104, 105, 104, 105, 105, 105, 105, 105, 104, 105, 104, 
103, 104, 103, 103, 103, 103, 102, 101, 101, 101, 100, 99, 99, 99, 98, 96, 
96, 95, 95, 93, 93, 92, 91, 90, 88, 88, 87, 86, 84, 83, 81, 81, 
80, 77, 76, 75, 74, 73, 72, 70, 69, 68, 67, 64, 64, 61, 60, 58, 
56, 54, 53, 52, 50, 48, 46, 44, 43, 41, 39, 37, 35, 33, 31, 29, 
28, 26, 25, 23, 21, 19, 17, 15, 13, 11, 9, 7, 6, 3, 1, -1, 
-3, -5, -7, -10, -11, -14, -15, -17, -19, -21, -23, -25, -27, -30, -32, -34, 
-36, -39, -42, -43, -45, -49, -50, -52, -55, -57, -59, -61, -63, -65, -67, -69, 
-72, -74, -75, -78, -80, -81, -83, -85, -88, -89, -90, -93, -94, -96, -98, -100, 
-100, -103, -104, -105, -105, -106, -108, -109, -111, -112, -112, -113, -115, -115, -115, -116, 
-117, -117, -117, -118, -117, -118, -118, -118, -118, -118, -118, -117, -117, -117, -117, -116, 
-116, -114, -114, -113, -112, -111, -110, -109, -107, -106, -104, -104, -103, -101, -100, -98, 
-96, -94, -92, -91, -88, -87, -85, -83, -80, -78, -76, -73, -71, -69, -67, -64, 
-62, -59, -58, -56, -53, -51, -48, -46, -43, -41, -39, -36, -34, -31, -30, -27, 
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
};

#endif /* sample0_H_ */
