lonesoulsurfer/Acid_Drip_Bassline_and_Drum_Synth/src/Acid_Drip_Drum_Acid_Drift_V5/sample4.h

#ifndef sample4_H_
#define sample4_H_
 
#if ARDUINO >= 100
#include "Arduino.h"
#else
#include "WProgram.h"
#endif
#include "mozzi_pgmspace.h"
 
#define sample4_NUM_CELLS 2737
#define sample4_SAMPLERATE 16384
 
CONSTTABLE_STORAGE(int8_t) sample4_DATA [] = {
0, 0, 1, 4, 5, 4, 4, 3, 4, -82, -125, -103, -76, -56, -53, -47, 
-49, -46, -39, -34, -29, -21, -16, -9, -1, 6, 13, 20, 25, 31, 37, 40, 
46, 48, 53, 54, 57, 57, 60, 58, 59, 57, 51, 53, 53, 50, 48, 46, 
46, 45, 45, 45, 45, 43, 44, 43, 43, 43, 42, 41, 43, 42, 41, 41, 
41, 39, 41, 39, 40, 40, 40, 39, 39, 35, 30, 30, 32, 34, 33, 35, 
29, 22, 22, 25, 27, 27, 19, 17, 18, 21, 19, 11, 11, 15, 16, 8, 
5, 9, 9, 3, 0, 4, 2, -3, -4, -1, -5, -10, -7, -7, -13, -14, 
-11, -14, -19, -17, -15, -22, -23, -19, -22, -27, -24, -24, -30, -29, -26, -30, 
-35, -31, -31, -36, -38, -35, -35, -42, -41, -38, -39, -45, -44, -41, -40, -46, 
-48, -47, -42, -43, -51, -51, -48, -44, -44, -50, -52, -51, -49, -46, -45, -45, 
-50, -53, -51, -48, -48, -46, -46, -45, -45, -44, -44, -44, -44, -44, -44, -48, 
-49, -46, -40, -38, -38, -39, -40, -40, -41, -40, -39, -39, -39, -39, -38, -32, 
-29, -29, -31, -29, -23, -22, -23, -18, -18, -14, -11, -10, -6, -4, -1, 2, 
5, 8, 12, 14, 16, 19, 20, 24, 25, 28, 29, 32, 34, 35, 38, 38, 
42, 40, 43, 44, 43, 47, 46, 44, 48, 50, 47, 43, 46, 50, 50, 47, 
45, 44, 43, 42, 46, 50, 50, 47, 45, 44, 44, 44, 43, 43, 42, 42, 
42, 41, 41, 41, 41, 40, 35, 31, 31, 33, 34, 35, 35, 35, 34, 33, 
29, 24, 24, 26, 27, 29, 27, 20, 19, 19, 20, 23, 18, 14, 13, 16, 
17, 11, 7, 10, 11, 8, 3, 4, 7, 4, -1, 0, 1, -2, -5, -4, 
-4, -7, -10, -9, -8, -12, -13, -13, -14, -19, -18, -16, -19, -22, -21, -21, 
-23, -24, -22, -24, -27, -28, -26, -28, -31, -32, -29, -30, -35, -36, -33, -32, 
-36, -39, -37, -34, -35, -40, -41, -40, -37, -36, -40, -43, -42, -41, -39, -38, 
-40, -45, -46, -44, -42, -40, -39, -39, -39, -39, -43, -46, -45, -44, -42, -41, 
-40, -39, -39, -39, -38, -38, -37, -38, -37, -37, -37, -37, -37, -34, -29, -26, 
-27, -28, -30, -30, -30, -24, -21, -21, -22, -20, -18, -16, -15, -12, -10, -7, 
-6, -3, -1, 2, 4, 7, 9, 11, 14, 16, 18, 20, 21, 23, 26, 27, 
29, 30, 32, 33, 34, 36, 38, 37, 40, 40, 39, 40, 42, 42, 40, 42, 
45, 44, 42, 39, 39, 42, 45, 46, 45, 42, 41, 39, 40, 39, 40, 39, 
38, 38, 38, 38, 37, 37, 36, 36, 36, 36, 36, 35, 35, 36, 34, 34, 
33, 28, 25, 25, 26, 28, 28, 28, 28, 24, 20, 20, 20, 22, 22, 20, 
16, 14, 16, 17, 17, 12, 9, 10, 12, 11, 7, 6, 6, 7, 4, 1, 
1, 3, 1, -2, -3, -3, -4, -7, -6, -7, -9, -11, -11, -10, -12, -14, 
-14, -14, -16, -18, -17, -18, -19, -21, -21, -20, -22, -24, -23, -23, -25, -26, 
-27, -25, -27, -29, -31, -28, -28, -31, -33, -33, -31, -30, -32, -35, -35, -34, 
-32, -32, -34, -37, -38, -37, -35, -34, -32, -33, -35, -39, -40, -39, -37, -36, 
-34, -35, -33, -33, -33, -34, -32, -32, -33, -31, -32, -31, -32, -31, -31, -31, 
-30, -30, -29, -30, -30, -29, -30, -27, -23, -21, -21, -21, -22, -20, -18, -16, 
-16, -14, -11, -11, -9, -7, -5, -3, -1, 2, 3, 5, 8, 8, 11, 13, 
16, 17, 18, 20, 21, 22, 24, 25, 27, 29, 29, 31, 32, 32, 33, 34, 
35, 37, 35, 35, 37, 38, 37, 35, 37, 39, 40, 40, 38, 36, 36, 34, 
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
};

#endif /* sample4_H_ */
