lonesoulsurfer/Acid_Drip_Bassline_and_Drum_Synth/src/Acid_Drip_Drum_Acid_Drift_V5/sample5.h

#ifndef sample5_H_
#define sample5_H_
 
#if ARDUINO >= 100
#include "Arduino.h"
#else
#include "WProgram.h"
#endif
#include "mozzi_pgmspace.h"
 
#define sample5_NUM_CELLS 3748
#define sample5_SAMPLERATE 16000
 
CONSTTABLE_STORAGE(int8_t) sample5_DATA [] = {
0, -1, 2, 38, 98, 119, 122, 123, 123, 116, 106, 96, 85, 73, 62, 50, 
39, 27, 11, -8, -23, -37, -48, -58, -67, -75, -83, -89, -96, -101, -106, -110, 
-114, -117, -119, -121, -121, -121, -121, -120, -118, -116, -113, -109, -106, -102, -97, -92, 
-86, -80, -74, -67, -61, -54, -46, -38, -31, -24, -16, -8, 0, 9, 17, 25, 
33, 41, 49, 57, 64, 72, 79, 85, 92, 98, 104, 109, 114, 118, 121, 124, 
125, 125, 125, 124, 124, 124, 124, 124, 123, 121, 118, 115, 110, 106, 101, 95, 
89, 83, 77, 71, 64, 58, 50, 43, 35, 27, 20, 12, 4, -4, -12, -20, 
-28, -36, -43, -50, -58, -65, -71, -78, -84, -90, -95, -100, -104, -109, -112, -115, 
-117, -119, -120, -120, -121, -120, -119, -117, -116, -113, -110, -107, -103, -99, -95, -89, 
-84, -80, -73, -68, -61, -56, -48, -42, -35, -28, -21, -13, -6, 1, 8, 15, 
23, 30, 37, 44, 50, 57, 63, 69, 74, 80, 85, 90, 94, 98, 101, 104, 
107, 108, 110, 110, 111, 110, 109, 108, 106, 104, 102, 99, 96, 92, 88, 83, 
79, 73, 68, 63, 56, 50, 44, 38, 32, 25, 19, 12, 5, -2, -8, -15, 
-22, -28, -35, -42, -48, -54, -60, -66, -71, -76, -81, -85, -89, -93, -96, -99, 
-101, -103, -105, -106, -106, -106, -106, -105, -103, -102, -99, -97, -93, -90, -86, -82, 
-78, -73, -68, -63, -58, -52, -46, -41, -35, -28, -22, -16, -10, -3, 4, 10, 
17, 23, 30, 36, 43, 48, 54, 60, 65, 70, 75, 79, 83, 87, 90, 93, 
95, 97, 98, 99, 99, 99, 98, 98, 97, 95, 93, 91, 88, 85, 82, 78, 
75, 70, 66, 62, 57, 52, 47, 42, 36, 30, 25, 19, 13, 8, 2, -4, 
-10, -15, -21, -27, -33, -38, -44, -49, -54, -59, -64, -68, -72, -76, -79, -82, 
-85, -87, -89, -91, -92, -92, -92, -92, -92, -90, -89, -87, -85, -83, -80, -77, 
-73, -70, -66, -62, -57, -53, -48, -43, -38, -33, -28, -22, -17, -11, -6, 1, 
6, 12, 17, 23, 28, 34, 39, 44, 49, 54, 58, 63, 66, 70, 74, 77, 
79, 82, 83, 85, 86, 87, 88, 87, 87, 87, 86, 84, 82, 80, 78, 75, 
72, 69, 65, 62, 57, 53, 49, 45, 40, 35, 30, 26, 20, 15, 10, 5, 
0, -5, -10, -15, -20, -25, -30, -34, -39, -43, -48, -52, -56, -60, -63, -66, 
-69, -71, -74, -76, -78, -79, -80, -81, -81, -81, -81, -80, -79, -78, -75, -74, 
-72, -69, -67, -64, -60, -57, -53, -49, -45, -41, -36, -32, -27, -22, -17, -12, 
-6, -2, 4, 9, 14, 19, 23, 28, 33, 38, 42, 46, 50, 53, 57, 60, 
63, 65, 67, 69, 71, 73, 74, 75, 76, 76, 76, 76, 75, 74, 73, 71, 
69, 67, 64, 61, 58, 55, 52, 48, 44, 41, 36, 33, 29, 25, 20, 16, 
11, 7, 3, -2, -7, -11, -15, -19, -23, -28, -32, -35, -40, -43, -46, -49, 
-53, -56, -58, -60, -62, -64, -65, -66, -67, -68, -69, -69, -69, -69, -68, -67, 
-67, -66, -64, -63, -60, -58, -56, -53, -50, -47, -43, -40, -36, -32, -28, -24, 
-20, -15, -11, -7, -2, 2, 7, 11, 15, 20, 24, 28, 32, 35, 39, 43, 
46, 50, 53, 55, 58, 60, 62, 64, 65, 66, 67, 67, 67, 68, 67, 66, 
66, 65, 63, 62, 60, 58, 56, 53, 50, 47, 44, 41, 38, 34, 31, 26, 
23, 19, 15, 12, 7, 3, 0, -4, -8, -12, -16, -20, -24, -27, -30, -34, 
-37, -41, -44, -46, -49, -52, -54, -56, -58, -59, -61, -62, -63, -63, -64, -64, 
-63, -62, -62, -60, -59, -58, -56, -54, -52, -49, -47, -44, -41, -38, -35, -31, 
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
};

#endif /* sample5_H_ */
