lonesoulsurfer/Acid_Drip_Bassline_and_Drum_Synth/src/Acid_Drip_Drum_Acid_Drift_V5/sample6.h

#ifndef sample6_H_
#define sample6_H_
 
#if ARDUINO >= 100
#include "Arduino.h"
#else
#include "WProgram.h"
#endif
#include "mozzi_pgmspace.h"
 
#define sample6_NUM_CELLS 3773
#define sample6_SAMPLERATE 16000
 
CONSTTABLE_STORAGE(int8_t) sample6_DATA [] = {
0, 0, 0, 1, 25, -70, -109, -52, -9, 17, 12, 21, 19, 8, 11, -2, 
31, 65, 19, -8, -14, -9, 5, 22, 10, -15, -4, 18, 13, -8, -27, -32, 
-24, -17, -13, -6, -4, 12, 18, 29, 39, 15, 5, -2, 2, -4, -11, -2, 
6, -6, -12, -8, -22, -21, -11, -6, 1, 5, 15, 22, 20, 8, 4, 2, 
-4, 0, -5, 2, -2, -9, -9, -8, -2, -4, 2, 7, 9, 4, 0, -3, 
-1, 0, -4, -2, 0, 4, 2, 0, 0, -1, 0, 1, 0, 0, -1, 0, 
1, 1, 0, -1, 2, -3, -4, -3, 1, 3, 4, 3, -2, -2, 1, -1, 
2, 3, 2, 1, -1, -2, -2, 0, 0, 2, 2, 0, 1, 2, 0, -1, 
-2, -2, -2, 1, 2, 3, 1, 1, -2, 1, 0, 1, 1, 1, -1, -2, 
0, 0, 0, 0, 2, 0, 2, -2, 0, -3, 2, -3, 5, -2, 7, -4, 
10, -7, 4, 78, -33, -109, -125, -73, -35, 34, 86, 59, 80, -6, -29, -55, 
-89, -53, -22, 38, 66, 61, 57, 28, -15, -44, -37, -27, -20, 21, 4, 14, 
18, -31, -21, -6, 27, 38, -1, -3, -11, 12, 8, -32, -9, 7, 18, 15, 
15, 3, -3, -7, 6, -8, -15, -13, -15, -5, -24, -8, 6, 15, 16, 18, 
20, 26, 20, 1, -13, -23, -34, -23, -9, -6, 15, 18, 10, 1, -3, 7, 
1, 0, 15, 6, -6, -3, -1, -2, -2, -2, 3, -3, -9, -8, -2, -2, 
4, 8, 2, 0, 3, 6, 5, 6, -3, -6, -6, -4, 3, 0, 4, 6, 
5, 2, -1, 0, 0, 2, -1, 0, 0, -1, -3, -8, -1, 1, 1, 4, 
4, 1, 3, 2, 0, -1, -5, -4, -1, 1, 4, 4, 0, 0, 2, 4, 
3, -1, -1, 0, -1, -1, -2, -1, 2, 2, 3, 4, 4, 1, -1, 0, 
1, 0, -1, -3, -2, -3, -2, -1, -1, -3, -1, 1, 3, 4, 6, 6, 
6, 4, 0, -2, -3, -1, -3, -1, -2, -1, -4, 1, -69, -73, -23, 37, 
117, 33, -18, 24, 27, 38, 34, -22, -10, -15, -22, -15, -49, -31, 4, 2, 
20, 11, -11, 21, -9, -20, -5, 18, 9, -3, 14, 25, 33, 36, 21, -24, 
-50, -47, -28, -3, -8, -14, -4, 22, 54, 28, 10, 10, 10, -6, -16, -19, 
-15, -2, 3, -4, -18, -17, -5, 5, 3, 8, 16, 19, 12, 24, 7, -3, 
-6, -16, -8, -15, -11, -3, 7, 2, -2, 9, 3, -5, 4, 12, 11, 8, 
0, -9, -9, -6, -8, -9, -7, -4, -5, -2, 2, 10, 6, 2, 2, -2, 
4, -2, -1, 4, 6, 4, 5, 3, 7, 6, 0, -6, -7, -1, -2, -2, 
3, 3, 3, 2, -2, -3, -2, -5, -9, -8, -8, -3, 0, 5, 5, 9, 
6, 9, 5, 4, 0, 3, 2, 2, 1, 0, -4, -6, -10, -98, -92, -46, 
47, 62, 68, 89, 9, 13, 1, 21, 3, -30, -27, -15, 26, 24, -42, -48, 
15, 23, -16, 2, 30, 18, -3, -13, -11, -25, -13, -13, -10, 33, 65, 20, 
8, 3, -30, -39, -16, 12, 10, -4, -27, -8, -26, -32, 11, -4, 8, 46, 
30, 24, 47, 34, 16, 4, -25, -42, -69, -62, -38, -2, 32, 1, -2, 34, 
37, 12, 29, 50, 31, 3, -12, -8, -39, -45, -34, -36, -31, -18, 16, 16, 
22, 30, 43, 24, 8, -2, -24, -7, -31, -26, -5, 22, 30, 11, 16, 10, 
3, -13, -12, 12, 7, -7, -21, -18, 0, -20, -5, 19, -5, -9, 10, 14, 
18, 34, 17, -31, -31, -4, -5, 15, 26, -9, -18, -19, -11, -1, -1, 9, 
-11, -5, 23, 18, 30, 21, 0, -13, -18, -3, -15, -10, -17, 10, 14, -13, 
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
};

#endif /* sample6_H_ */
