lonesoulsurfer/Acid_Drip_Bassline_and_Drum_Synth/src/Acid_Drip_Drum_Acid_Drift_V5/sample1.h

#ifndef sample1_H_
#define sample1_H_
 
#if ARDUINO >= 100
#include "Arduino.h"
#else
#include "WProgram.h"
#endif
#include "mozzi_pgmspace.h"
 
#define sample1_NUM_CELLS 1526
#define sample1_SAMPLERATE 16384
 
CONSTTABLE_STORAGE(int8_t) sample1_DATA [] = {
0, 0, 7, -4, -6, 3, -6, -4, 15, -16, 5, 11, -10, -8, 19, -12, 
7, -6, -20, 51, -35, 3, 11, -27, 40, -39, 17, 9, -43, 53, -41, 19, 
-12, 5, 5, -4, -2, -4, 17, -14, 7, 0, -6, 0, 9, -16, 28, -14, 
-2, 11, -8, 7, -2, -10, 17, -14, 0, 0, 28, -39, 17, -8, -4, 13, 
-25, 30, -43, 34, -16, -23, 32, -6, -31, 51, -54, 38, -29, -20, 99, -87, 
42, -20, -4, 32, -27, -12, 21, 0, -39, 74, -104, 86, -33, -39, 80, -125, 
97, -83, 28, 17, -43, -12, 28, 3, -60, 90, -75, 34, -18, 11, 11, -92, 
97, -94, 42, -8, -14, -6, 28, 21, -66, 67, -75, 78, -89, 0, -10, -73, 
72, -62, 21, -25, 40, -33, -8, 65, -104, 55, -43, 23, -48, 51, 11, -66, 
53, -20, -8, -8, 47, -81, 97, -66, 15, 17, -8, -2, -33, 49, -60, 38, 
-10, 5, 26, -48, 51, -25, -23, 61, -37, -18, 30, 13, -31, 17, 13, -23, 
0, 36, -64, 53, -23, -4, 36, -48, 49, -100, 49, -25, -54, 86, -83, 51, 
-33, 13, -23, -10, 15, -31, 15, -16, 44, -54, 38, -6, 23, -58, 63, -6, 
-48, 53, -23, 19, -64, 30, -23, -52, 74, -87, 59, -8, -41, 53, -71, 55, 
-69, 26, 0, -10, -12, 17, 26, -52, 61, -14, -35, 49, -64, 53, -33, -10, 
53, -66, 49, 0, -58, 34, -8, -62, 74, -79, 72, -48, 7, 21, -50, 61, 
-60, 7, 34, -33, -12, 34, 17, -33, 13, 23, -31, 26, -31, 55, -56, 13, 
21, -62, 72, -48, -10, 42, -41, 26, -33, 11, 17, -60, 72, -23, -29, 61, 
-60, 34, -2, -4, 0, -43, 63, -64, 17, 30, -46, 34, -4, 13, -14, -14, 
47, -46, 34, 0, 0, -18, -4, 32, -60, 61, -27, -20, 57, -52, 38, -23, 
-4, 28, -46, 44, -27, -2, 32, -27, 32, -16, 17, -8, -29, 57, -66, 42, 
-8, -10, 30, -31, 26, 26, -46, 42, -20, -16, 40, -66, 53, -41, 32, -23, 
23, 9, -29, 32, -35, 44, -39, 21, 0, -33, 61, -66, 36, -12, -10, 34, 
-39, 21, -4, -14, 17, 11, -41, 44, -39, 23, -2, -6, 40, -56, 36, -8, 
-20, 38, -29, 9, 11, 7, -29, 36, -2, -35, 36, -37, 23, -20, 9, 11, 
-16, 3, 15, -20, 23, -4, -6, 9, 3, 5, -23, 38, -12, -16, 13, 7, 
0, -6, 19, -10, -4, 19, -33, 11, 11, -10, -4, 17, -6, -14, 17, 11, 
-29, 26, -2, -23, 23, -8, 3, -2, -18, 23, -23, 19, -12, -2, 13, -14, 
23, -33, 38, -29, 5, 15, -10, -14, 9, 11, -33, 34, -10, -18, 28, -14, 
9, -12, 15, -8, -12, 23, -4, -12, 3, 17, -31, 47, -37, 15, 7, -20, 
15, 3, -8, 0, 11, -10, 5, 5, -10, 15, -8, -4, 17, -18, 15, -4, 
9, -20, 21, -18, 15, -4, -2, 13, -25, 34, -27, 7, 7, -20, 17, -4, 
-12, 17, -12, 3, 11, -16, 7, -6, -2, 15, -20, 15, -10, 3, 7, -16, 
15, 9, -25, 11, 5, -23, 28, -8, -16, 30, -27, 9, 7, -18, 30, -29, 
17, 3, -23, 26, -18, 0, 17, -16, 9, -10, 15, -2, -10, 17, -12, 3, 
0, 13, -14, -6, 23, -27, 17, -2, 9, -10, 5, 9, -27, 34, -25, 3, 
11, -8, -6, 11, -10, 7, 5, 0, 3, -18, 26, -14, 0, 13, -23, 21, 
-14, 11, -8, -8, 23, -35, 30, -12, 7, -14, 7, 11, -23, 26, -23, 11, 
5, -10, 0, -4, 21, -18, 3, 9, -4, -14, 19, -4, -8, 5, -8, 17, 
-18, 19, -25, 17, -4, -10, 17, -20, 21, -18, 7, 11, -23, 19, -2, -12, 
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
};

#endif /* sample1_H_ */
