lonesoulsurfer/Acid_Drip_Bassline_and_Drum_Synth/src/Acid_Drip_Drum_Acid_Drift_V5/sample2.h

#ifndef sample2_H_
#define sample2_H_
 
#if ARDUINO >= 100
#include "Arduino.h"
#else
#include "WProgram.h"
#endif
#include "mozzi_pgmspace.h"
 
#define sample2_NUM_CELLS 2200
#define sample2_SAMPLERATE 16384
 
CONSTTABLE_STORAGE(int8_t) sample2_DATA [] = {
0, -1, 5, 15, -15, -26, -25, -9, 2, 13, 14, 15, 21, 14, 6, 1, 
5, 1, -2, -14, -14, -10, -19, -25, -25, -19, -10, -6, 6, 12, 3, -3, 
-3, 12, 26, 24, 13, -1, -7, -10, -8, 1, 6, 9, 16, 20, 24, 25, 
15, 16, 21, 24, 17, 8, -1, -6, -8, -33, -26, -13, -30, -11, -7, -27, 
-10, -3, -26, -17, 15, -17, -34, -16, -19, -22, -21, -16, -5, -1, -5, -5, 
-13, -34, -8, 29, 14, 0, -1, -25, -24, 21, 47, 39, 23, 32, 46, 41, 
31, 28, 22, 20, 17, 12, 10, 9, -16, -27, -15, -2, 2, -21, -15, -10, 
-21, -6, 3, 10, 20, 22, 23, 29, 26, 13, 6, 6, 7, -15, -3, 6, 
-16, -34, -18, 0, -3, 30, 20, 26, 52, 34, 29, 34, 1, -8, 10, 41, 
5, -11, 23, -22, -39, -63, -72, -64, -48, -22, -27, -16, -32, -77, -92, -71, 
-72, -44, -8, -80, -125, -70, -38, -100, -118, -39, -8, -93, -87, 6, 5, -32, 
-38, -11, 22, 37, 28, 39, 49, 53, 55, 48, 60, 55, 51, 52, 31, 49, 
54, 38, 52, 59, 32, 21, 51, 63, 54, 42, 45, 49, 49, 32, 36, 33, 
25, 26, 47, 47, 39, 47, 59, 28, -8, 8, 47, 15, -38, 26, 37, 31, 
21, 0, 29, 31, 5, 28, 45, -56, -116, -69, -1, 5, -55, 3, 9, -53, 
-69, -61, -50, -94, -101, -103, -100, -104, -123, -105, -66, -92, -115, -95, -95, -64, 
-76, -108, -97, -103, -26, -40, -104, -88, -95, -81, -66, -33, 24, 7, -66, -45, 
3, 41, -10, -36, 32, 49, 40, 47, 31, 40, 75, 67, 60, 49, 64, 73, 
69, 62, 76, 76, 65, 59, 62, 77, 64, 54, 73, 81, 69, 51, 65, 73, 
60, 47, 41, 46, 57, 68, 46, 47, 46, 29, -7, 14, 49, 16, -9, -1, 
31, 65, 6, -57, 18, 39, -16, -62, -54, 3, 26, -37, -58, -14, 20, -46, 
-115, -29, 29, -55, -114, -65, -31, -44, -75, -72, -85, -72, -80, -86, -63, -75, 
-87, -93, -87, -79, 10, -6, -76, -46, -10, -13, -48, -68, -3, -26, -85, -37, 
-27, -42, 12, 52, -2, -21, -32, 18, 48, 31, 14, 32, 40, -6, 39, 49, 
24, 31, 55, 69, 52, 62, 64, 46, 56, 21, 25, 52, 55, 45, 41, 53, 
41, 1, -15, 60, 32, 7, -15, -1, 33, -17, -1, 15, 13, -39, -30, 51, 
65, 6, -31, 33, -19, -56, -7, 1, 42, 30, -3, -18, -24, 37, 39, -9, 
10, 24, -11, -11, -16, 6, 48, -7, -1, 29, 8, 10, 5, 37, 13, -38, 
-3, 32, 9, -26, 12, 38, 9, 29, 8, 13, 29, 38, 24, 1, 30, 15, 
28, 23, 23, 14, 1, -13, -11, 52, 13, -1, 22, 37, 30, 9, 8, 12, 
46, 31, 10, 7, 51, -9, -23, 40, 12, 10, 36, 55, 18, -19, -13, 15, 
37, 14, 2, 17, -5, 8, -1, -22, 22, 16, 18, 15, -24, -7, -9, -6, 
2, -22, 7, 5, -46, -19, -11, -25, -25, -6, -10, -45, -33, 8, -26, -75, 
-46, -6, 0, -32, -32, -31, -17, -13, -33, -48, -14, -40, -41, -27, -29, -5, 
-7, 7, 1, -29, -9, 25, 9, 9, -19, 15, 38, 16, 3, -17, 2, 8, 
-10, 12, 18, 13, 53, 31, 12, 13, 2, 20, 46, 12, -5, 9, -10, 28, 
40, 6, 23, 48, 44, -6, -31, 15, 9, 28, 46, 22, 16, 30, 25, -2, 
29, 30, 17, 7, 17, 37, 26, 16, 6, 2, 21, 40, -2, -5, 10, 5, 
18, 18, -7, 9, 16, 2, 7, -8, -3, 2, 9, 6, 5, 3, -1, 5, 
6, 6, -10, -19, 9, 18, 13, 5, -3, 13, 20, 16, 0, 5, 9, 13, 
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
};

#endif /* sample2_H_ */
