lonesoulsurfer/Acid_Drip_Bassline_and_Drum_Synth/src/Acid_Drip_Drum_Acid_Drift_V5/sample7.h

#ifndef sample7_H_
#define sample7_H_
 
#if ARDUINO >= 100
#include "Arduino.h"
#else
#include "WProgram.h"
#endif
#include "mozzi_pgmspace.h"
 
#define sample7_NUM_CELLS 2134
#define sample7_SAMPLERATE 16000
 
CONSTTABLE_STORAGE(int8_t) sample7_DATA [] = {
0, -7, 6, 25, -12, -13, 0, -18, 14, -8, -7, 20, -28, 68, -50, -3, 
38, 3, -10, 9, 35, -35, 20, -35, -12, 60, -52, 42, 33, -12, -12, 22, 
60, -6, 45, 21, 33, 14, 50, 25, 29, 36, 49, 18, 59, 8, 26, -13, 
-36, 125, -38, 10, -16, 50, 43, 5, 18, -42, 36, -39, -66, 29, 7, -1, 
-7, 7, -17, -33, 43, -75, 13, 40, -28, -15, 3, 29, -19, -27, -1, -6, 
-2, -3, -9, 21, 8, 61, -13, 37, 30, -39, -8, -40, -6, -31, 4, -8, 
6, 36, 30, 14, 2, 72, 44, -1, 32, 41, 4, 5, 15, -6, 22, -2, 
-54, 18, 4, -35, -14, -6, 1, -50, -10, -4, -7, 7, -32, -5, -23, 4, 
-29, -8, 61, -32, -8, 10, -1, 23, -24, 33, 33, -15, 17, 6, 24, 35, 
-7, -5, 59, 0, -21, 24, -8, 3, -17, -12, 42, 6, -15, -21, -4, 3, 
-47, -28, -8, -21, -41, 14, 38, -16, 4, -1, -4, 6, 0, -21, 19, 44, 
5, 15, -7, 44, -13, -7, 63, -8, -14, -1, -16, 10, -12, -30, 16, 0, 
-13, -31, -1, -17, -7, -8, -33, -9, -33, -5, -9, -20, 28, -4, -23, 14, 
-8, 8, 9, -22, 61, -4, -24, 16, -11, -17, -19, 6, -16, -23, -25, 17, 
-7, 4, 17, 25, -10, 6, 28, -7, 24, -16, 39, -8, -35, 38, -2, 6, 
1, 23, 7, -5, -19, 15, -1, -29, 44, -33, 27, 2, -23, 32, -31, -26, 
13, 6, -9, 10, 8, 0, 43, -14, -2, 35, -23, 12, 10, 1, 0, -16, 
-7, -6, -14, 16, -1, 10, 42, -16, -34, 20, 2, -13, -16, -11, -12, -2, 
-16, -31, -19, -12, -29, 1, -10, -18, 25, -32, 10, -18, -21, 9, 24, -24, 
-4, 25, -21, 9, 15, -20, -16, 19, 2, -4, 0, 22, -18, 27, -11, -14, 
-2, 12, -3, -11, 23, -22, 46, 9, -1, 37, -3, 0, 30, 7, 29, -34, 
-5, 35, -22, -5, 12, 7, -16, 4, -20, -9, -4, -15, -13, -6, 14, -2, 
-15, 2, -19, 9, 3, -20, 5, 23, 10, 2, 23, 1, -20, 23, 16, -26, 
14, -20, -1, -1, 5, -6, 6, 6, 6, 23, -18, 2, -18, -8, -11, -23, 
0, 11, -20, -8, 2, 17, -17, -9, -17, -21, 9, -19, 12, -38, 16, 5, 
-17, 24, -24, 5, 1, 22, -14, 14, 20, -7, 34, -9, -5, -16, 39, 10, 
-25, 12, -12, 0, -1, -25, -11, -14, 24, 1, 0, 27, -14, -10, 5, 7, 
-26, 20, -1, -9, 3, 7, -19, -11, -3, -9, -21, 11, 14, -21, 6, -20, 
-13, -9, 18, -19, 5, 16, -10, 26, 11, -16, 32, 4, 3, -10, 3, 14, 
-18, -5, -27, -10, -20, 10, -34, -8, 5, -12, 19, -15, -13, -6, -12, 6, 
6, -13, 9, 14, -2, -4, 4, -11, -7, -2, -29, 17, -4, -8, -17, -18, 
-7, 4, 21, -19, 14, -2, 11, -10, 13, 8, -7, -4, 18, 3, -9, 19, 
-6, 2, -8, -7, -19, 5, -16, 3, -10, -8, 9, -8, 10, -14, -8, 12, 
-9, -1, -5, -6, -17, -6, -5, -7, 6, -16, 15, -23, 14, 10, -14, 9, 
3, -18, 17, -2, -17, 10, -4, -6, -11, 29, -6, 4, -8, 2, -6, 4, 
15, -8, -11, -12, -11, -8, -16, 6, 3, -3, 17, -25, 15, -27, 24, -17, 
-16, 23, -25, 21, 0, 17, 7, -1, -2, -7, 5, 18, -1, 8, 1, -13, 
8, -1, -2, 11, -18, -8, 16, -12, -15, -4, 9, 6, 19, -9, -1, -3, 
-13, 11, -15, 0, 13, -22, 16, 6, -20, -1, -9, 17, -12, -8, 4, 4, 
-12, -14, 4, 3, 3, -19, -12, -12, 5, 4, 3, 2, -10, 10, -17, -2, 
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
};

#endif /* sample7_H_ */
