lonesoulsurfer/Acid_Drip_Bassline_and_Drum_Synth/src/Acid_Drip_Drum_Acid_Drift_V5/sample3.h

#ifndef sample3_H_
#define sample3_H_
 
#if ARDUINO >= 100
#include "Arduino.h"
#else
#include "WProgram.h"
#endif
#include "mozzi_pgmspace.h"
 
#define sample3_NUM_CELLS 426
#define sample3_SAMPLERATE 16384
 
CONSTTABLE_STORAGE(int8_t) sample3_DATA [] = {
0, 1, -5, -10, 4, 6, 5, 6, -3, -55, -44, -37, -15, 49, 63, 48, 
58, -14, -46, -34, -19, -19, 17, 80, 75, 44, -59, -35, -22, -21, -18, 22, 
81, 44, 54, -6, -125, -54, -39, -4, 57, 30, 40, 12, 27, -49, -86, -59, 
-25, 32, 28, 24, 26, -22, -54, -34, -27, -13, -8, 13, 30, 15, 17, 18, 
21, 18, 21, 14, 54, 77, 51, -1, -107, -63, -21, 15, 45, 28, 22, 8, 
0, -12, -27, -46, -26, -28, -25, -25, -18, -39, -59, -40, -27, -9, 4, 19, 
27, 36, 39, 42, 40, 39, 33, 30, 23, 23, 17, 10, -5, -10, -4, 4, 
27, 22, 9, -5, -14, -26, -32, -36, -39, -39, -36, -34, -27, -30, -41, -34, 
-21, -8, 6, 17, 26, 32, 37, 39, 39, 37, 32, 28, 23, 17, 13, 8, 
3, -1, -3, -4, 0, 5, 9, 4, -5, -13, -19, -25, -27, -28, -28, -27, 
-25, -27, -27, -23, -17, -9, -1, 8, 13, 19, 24, 27, 27, 28, 26, 24, 
19, 17, 13, 9, 5, 3, -1, -1, -3, -3, -4, -5, -4, -5, -6, -8, 
-9, -12, -14, -15, -17, -18, -18, -15, -13, -12, -6, -3, 3, 6, 10, 13, 
15, 15, 17, 17, 14, 13, 12, 10, 8, 5, 3, 3, 0, -1, -3, -3, 
-4, -4, -4, -5, -6, -8, -9, -9, -8, -9, -9, -10, -9, -8, -6, -4, 
-1, 1, 3, 5, 6, 8, 8, 9, 9, 9, 8, 6, 5, 5, 5, 4, 
3, 0, 1, 0, -1, -1, -3, -4, -3, -4, -5, -5, -5, -5, -6, -5, 
-5, -5, -4, -3, -1, -1, 0, 3, 3, 3, 4, 5, 5, 5, 5, 5, 
5, 5, 4, 3, 4, 3, 1, 1, 1, 0, -1, -1, -3, -1, -3, -4, 
-4, -4, -4, -4, -4, -4, -4, -3, -3, -3, -1, 0, 0, 0, 1, 3, 
3, 4, 4, 4, 4, 3, 4, 4, 4, 1, 1, 1, 1, 0, 0, 0, 
-1, -1, -1, -1, -3, -4, -3, -3, -4, -4, -3, -3, -1, -1, 0, 0, 
0, 0, 1, 1, 1, 1, 3, 3, 3, 3, 3, 1, 1, 0, 0, 0, 
0, 0, -1, -1, -1, -1, -1, -1, -1, -1, -1, -1, -1, 0, -1, 0, 
1, 0, 0, 1, 0, 1, 1, 1, 0, 1, 0, 0, 0, 1, 0, -1, 
0, 0, 0, 0, 0, 0, 0, 0, 0, 0, 0, 0, 0, 0, 0, 0, 
0, 0, 0, 0, 0, 0, 0, 0, 0, 0, 
};

#endif /* sample3_H_ */
